Ixox/preenfm2/src/synth/Timbre.cpp

/*
 * Copyright 2013 Xavier Hosxe
 *
 * Author: Xavier Hosxe (xavier <.> hosxe < a t > gmail.com)
 *
 * This program is free software: you can redistribute it and/or modify
 * it under the terms of the GNU General Public License as published by
 * the Free Software Foundation, either version 3 of the License, or
 * (at your option) any later version.
 * This program is distributed in the hope that it will be useful,
 * but WITHOUT ANY WARRANTY; without even the implied warranty of
 * MERCHANTABILITY or FITNESS FOR A PARTICULAR PURPOSE.  See the
 * GNU General Public License for more details.
 * You should have received a copy of the GNU General Public License
 * along with this program.  If not, see <http://www.gnu.org/licenses/>.
 */


#include <math.h>
#include "Timbre.h"
#include "Voice.h"

#define INV127 .00787401574803149606f
#define INV16 .0625f
#define filterWindowMin 0.01f
#define filterWindowMax 0.99f
// Regular memory
float midiNoteScale[2][NUMBER_OF_TIMBRES][128];

float Timbre::unisonPhase[14] = { .37f, .11f, .495f, .53f, .03f, .19f, .89f, 0.23f, .71f, .19f, .31f, .43f, .59f, .97f };

/*
#include "LiquidCrystal.h"
extern LiquidCrystal lcd;
void myVoiceError(char info, int t, int t2) {
    lcd.setRealTimeAction(true);
    lcd.clear();
    lcd.setCursor(0,0);
    lcd.print('!');
    lcd.print(info);
    lcd.print(t);
    lcd.print(' ');
    lcd.print(t2);
    while (true) {};
}

...
        if (voiceNumber[k] < 0) myVoiceError('A', voiceNumber[k], k);

*/

//#define DEBUG_ARP_STEP
enum ArpeggiatorDirection {
    ARPEGGIO_DIRECTION_UP = 0,
    ARPEGGIO_DIRECTION_DOWN,
    ARPEGGIO_DIRECTION_UP_DOWN,
    ARPEGGIO_DIRECTION_PLAYED,
    ARPEGGIO_DIRECTION_RANDOM,
    ARPEGGIO_DIRECTION_CHORD,
   /*
    * ROTATE modes rotate the first note played, e.g. UP: C-E-G -> E-G-C -> G-C-E -> repeat
    */
    ARPEGGIO_DIRECTION_ROTATE_UP, ARPEGGIO_DIRECTION_ROTATE_DOWN, ARPEGGIO_DIRECTION_ROTATE_UP_DOWN,
   /*
    * SHIFT modes rotate and extend with transpose, e.g. UP: C-E-G -> E-G-C1 -> G-C1-E1 -> repeat
    */
    ARPEGGIO_DIRECTION_SHIFT_UP, ARPEGGIO_DIRECTION_SHIFT_DOWN, ARPEGGIO_DIRECTION_SHIFT_UP_DOWN,

    ARPEGGIO_DIRECTION_COUNT
};

// TODO Maybe add something like struct ArpDirectionParams { dir, can_change, use_start_step }

inline static int __getDirection( int _direction ) {
	switch( _direction ) {
	case ARPEGGIO_DIRECTION_DOWN:
	case ARPEGGIO_DIRECTION_ROTATE_DOWN:
	case ARPEGGIO_DIRECTION_SHIFT_DOWN:
		return -1;
	default:
		return 1;
	}
}

inline static int __canChangeDir( int _direction ) {
	switch( _direction ) {
	case ARPEGGIO_DIRECTION_UP_DOWN:
	case ARPEGGIO_DIRECTION_ROTATE_UP_DOWN:
	case ARPEGGIO_DIRECTION_SHIFT_UP_DOWN:
		return 1;
	default:
		return 0;
	}
}

inline static int __canTranspose( int _direction ) {
	switch( _direction ) {
	case ARPEGGIO_DIRECTION_SHIFT_UP:
	case ARPEGGIO_DIRECTION_SHIFT_DOWN:
	case ARPEGGIO_DIRECTION_SHIFT_UP_DOWN:
		return 1;
	default:
		return 0;
	}
}

//for bitwise manipulations
#define FLOAT2SHORT 32768.f
#define SHORT2FLOAT 1./32768.f

#define RATIOINV 1./131072.f

#define SVFRANGE 1.23f
#define SVFOFFSET 0.151f
#define SVFGAINOFFSET 0.3f

#define LP2OFFSET -0.045f
#define min(a,b)                ((a)<(b)?(a):(b))
#define PIINV 0.318309886183791f

extern float noise[32];

inline 
float expf_fast(float a) {
  //https://github.com/ekmett/approximate/blob/master/cbits/fast.c
  union { float f; int x; } u;
  u.x = (int) (12102203 * a + 1064866805);
  return u.f;
}
inline
float sqrt3(const float x)  
{
  union
  {
    int i;
    float x;
  } u;

  u.x = x;
  u.i = (1 << 29) + (u.i >> 1) - (1 << 22);
  return u.x;
} 
inline
float tanh3(float x)
{
	//return x / (0.7f + fabsf(0.8f * x));
	return 1.5f * x / (1.7f + fabsf(0.34f * x * x));
}
inline
float tanh4(float x)
{
	return x / sqrt3(x * x + 1);
}
inline
float sat25(float x)
{ 
	if (unlikely(fabsf(x) > 4))
		return 0;
	return x * (1.f - fabsf(x * 0.25f));
}
inline
float sat66(float x)
{
	return x * (1 - (x * x * 0.055f));
}
inline
float sat33(float x)
{
	if (unlikely(fabsf(x) > 2.58f))
		return 0;
	return x * (1 - x * x * 0.15f);
}
inline
float clamp(float d, float min, float max) {
  const float t = unlikely(d < min) ? min : d;
  return unlikely(t > max) ? max : t;
}
inline 
float satSin(float x, float drive, uint_fast16_t pos) {
	//https://www.desmos.com/calculator/pdsqpi5lp6
	return x + clamp(x, -0.5f * drive, drive) * sinTable[((uint_fast16_t)(fabsf(x) * 360) + pos) & 0x3FF];
}
inline 
float fastSin(float x) {
	return sinTable[(int)(fabsf(x * PIINV) * 2048)  & 0x7FF] * 0.5f;
}
//https://www.musicdsp.org/en/latest/Other/120-saturation.html
inline
float sigmoid(float x)
{
	return x * (1.5f - 0.5f * x * x);
}
inline
float sigmoidPos(float x)
{
	//x : 0 -> 1
	return (sigmoid((x * 2) - 1) + 1) * 0.5f;
}
inline
float fold(float x4) {
	// https://www.desmos.com/calculator/ge2wvg2wgj
	// x4 = x / 4
	return (fabsf(x4 + 0.25f - roundf(x4 + 0.25f)) - 0.25f);
}
inline
float foldPos(float x) {
	return fold(((x * 2) - 1) * 0.25f) * 2 + 0.5f;
}
inline
float wrap(float x) {
	return x - floorf(x);
}
inline
float wrapBipolar(float x) {
	const float a = fabsf(x);
	return copysignf(a - floorf(a), x);
}
inline 
float window(float x) {
	if (x < 0 || x > 1) {
		return 0;
	} else if (x < 0.2f) {
		return sqrt3( x * 5 );
	} else if (x > 0.8f) {
		return sqrt3(1 - (x-0.8f) * 5);
	} else {
		return 1;
	}
}
inline float ftan(float fAngle)
{
	float fASqr = fAngle * fAngle;
	float fResult = 2.033e-01f;
	fResult *= fASqr;
	fResult += 3.1755e-01f;
	fResult *= fASqr;
	fResult += 1.0f;
	fResult *= fAngle;
	return fResult;
}
enum NewNoteType {
	NEW_NOTE_FREE = 0,
	NEW_NOTE_RELEASE,
	NEW_NOTE_OLD,
	NEW_NOTE_NONE
};
//TB303 filter emulation ------
const float filterpoles[10][64] = {
	{-1.42475857e-02, -1.10558351e-02, -9.58097367e-03,
	 -8.63568249e-03, -7.94942757e-03, -7.41570560e-03,
	 -6.98187179e-03, -6.61819537e-03, -6.30631927e-03,
	 -6.03415378e-03, -5.79333654e-03, -5.57785533e-03,
	 -5.38325013e-03, -5.20612558e-03, -5.04383985e-03,
	 -4.89429884e-03, -4.75581571e-03, -4.62701254e-03,
	 -4.50674977e-03, -4.39407460e-03, -4.28818259e-03,
	 -4.18838855e-03, -4.09410427e-03, -4.00482112e-03,
	 -3.92009643e-03, -3.83954259e-03, -3.76281836e-03,
	 -3.68962181e-03, -3.61968451e-03, -3.55276681e-03,
	 -3.48865386e-03, -3.42715236e-03, -3.36808777e-03,
	 -3.31130196e-03, -3.25665127e-03, -3.20400476e-03,
	 -3.15324279e-03, -3.10425577e-03, -3.05694308e-03,
	 -3.01121207e-03, -2.96697733e-03, -2.92415989e-03,
	 -2.88268665e-03, -2.84248977e-03, -2.80350622e-03,
	 -2.76567732e-03, -2.72894836e-03, -2.69326825e-03,
	 -2.65858922e-03, -2.62486654e-03, -2.59205824e-03,
	 -2.56012496e-03, -2.52902967e-03, -2.49873752e-03,
	 -2.46921570e-03, -2.44043324e-03, -2.41236091e-03,
	 -2.38497108e-03, -2.35823762e-03, -2.33213577e-03,
	 -2.30664208e-03, -2.28173430e-03, -2.25739130e-03,
	 -2.23359302e-03},
	{1.63323670e-16, -1.61447133e-02, -1.99932070e-02,
	 -2.09872000e-02, -2.09377795e-02, -2.04470150e-02,
	 -1.97637613e-02, -1.90036975e-02, -1.82242987e-02,
	 -1.74550383e-02, -1.67110053e-02, -1.59995606e-02,
	 -1.53237941e-02, -1.46844019e-02, -1.40807436e-02,
	 -1.35114504e-02, -1.29747831e-02, -1.24688429e-02,
	 -1.19916965e-02, -1.15414484e-02, -1.11162818e-02,
	 -1.07144801e-02, -1.03344362e-02, -9.97465446e-03,
	 -9.63374867e-03, -9.31043725e-03, -9.00353710e-03,
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


    // Init FX variables
	v0L = v1L = v2L = v3L = v4L = v5L = v6L = v7L = v8L = v0R = v1R = v2R = v3R = v4R = v5R = v6R = v7R = v8R = v8R = 0.0f;
	fxParamA1 = fxParamA2 = fxParamB2 = 0;
    fxParam1PlusMatrix = -1.0;

	// Center balance
	leftRightBalance = .5f;

}

Timbre::~Timbre() {
}

void Timbre::init(int timbreNumber, SynthState* sState) {


	env1.init(&params.env1a,  &params.env1b, 0, &params.engine1.algo);
	env2.init(&params.env2a,  &params.env2b, 1, &params.engine1.algo);
	env3.init(&params.env3a,  &params.env3b, 2, &params.engine1.algo);
	env4.init(&params.env4a,  &params.env4b, 3, &params.engine1.algo);
	env5.init(&params.env5a,  &params.env5b, 4, &params.engine1.algo);
	env6.init(&params.env6a,  &params.env6b, 5, &params.engine1.algo);

	osc1.init(sState, &params.osc1, OSC1_FREQ);
	osc2.init(sState, &params.osc2, OSC2_FREQ);
	osc3.init(sState, &params.osc3, OSC3_FREQ);
	osc4.init(sState, &params.osc4, OSC4_FREQ);
	osc5.init(sState, &params.osc5, OSC5_FREQ);
	osc6.init(sState, &params.osc6, OSC6_FREQ);

    this->timbreNumber = timbreNumber;

    for (int s=0; s<2; s++) {
        for (int n=0; n<128; n++) {
            midiNoteScale[s][timbreNumber][n] = INV127 * (float)n;
        }
    }
    for (int lfo=0; lfo<NUMBER_OF_LFO; lfo++) {
        lfoUSed[lfo] = 0;
    }

}

void Timbre::setVoiceNumber(int v, int n) {
	voiceNumber[v] = n;
	if (n >=0) {
		voices[n]->setCurrentTimbre(this);
	}
}


void Timbre::initVoicePointer(int n, Voice* voice) {
	voices[n] = voice;
}

void Timbre::noteOn(uint8_t note, uint8_t velocity) {
	if (params.engineArp1.clock) {
		arpeggiatorNoteOn(note, velocity);
	} else {
		preenNoteOn(note, velocity);
	}
}

void Timbre::noteOff(uint8_t note) {
	if (params.engineArp1.clock) {
		arpeggiatorNoteOff(note);
	} else {
		preenNoteOff(note);
	}
}

int cptHighNote = 0;

void Timbre::preenNoteOn(uint8_t note, uint8_t velocity) {

	this->lastVelocity = velocity * INV127;
	bool isUnison = params.engine1.numberOfVoice > 1  && params.engine2.playMode == 2.0f;

	int iNov;
	if (likely(!isUnison)) {
		iNov = (int) params.engine1.numberOfVoice;
	} else {
		iNov = 1;
	}

	if (unlikely(iNov == 0)) {
		return;
	}

	unsigned int indexMin = (unsigned int)2147483647;
	int voiceToUse = -1;

	int newNoteType = NEW_NOTE_NONE;

	for (int k = 0; k < iNov; k++) {
		// voice number k of timbre
		int n = voiceNumber[k];

        if (unlikely(voices[n]->isNewNotePending())) {
            continue;
        }

		// same note = priority 1 : take the voice immediatly
		if (unlikely(voices[n]->isPlaying() && voices[n]->getNote() == note)) {

#ifdef DEBUG_VOICE
		lcd.setRealTimeAction(true);
		lcd.setCursor(16,1);
		lcd.print(cptHighNote++);
		lcd.setCursor(16,2);
		lcd.print("S:");
		lcd.print(n);
#endif
			if (!isUnison) {
				preenNoteOnUpdateMatrix(n, note, velocity);
				voices[n]->noteOnWithoutPop(note, velocity, voiceIndex++);
			} else {
				float noteFrequencyUnison = (1 - params.engine2.unisonDetune * .05f);
				float noteFrequencyUnisonInc =  params.engine2.unisonDetune * numberOfVoiceInverse * .1f;

                for (int k = 0; k < params.engine1.numberOfVoice; k++) {
                    int n = voiceNumber[k];
                    preenNoteOnUpdateMatrix(n, note, velocity);
                    voices[n]->noteOnWithoutPop(note, velocity, voiceIndex++, noteFrequencyUnison, unisonPhase[k]);
					noteFrequencyUnison += noteFrequencyUnisonInc;
                }
			}
			this->lastPlayedVoiceNum = n;
			return;
		}

		// unlikely because if it true, CPU is not full
		if (unlikely(newNoteType > NEW_NOTE_FREE)) {
			if (!voices[n]->isPlaying()) {
				voiceToUse = n;
				newNoteType = NEW_NOTE_FREE;
			} else if (voices[n]->isReleased()) {
				int indexVoice = voices[n]->getIndex();
				if (indexVoice < indexMin) {
					indexMin = indexVoice;
					voiceToUse = n;
					newNoteType = NEW_NOTE_RELEASE;
				}
			}
		}
	}

	if (voiceToUse == -1) {
		for (int k = 0; k < iNov; k++) {
			// voice number k of timbre
			int n = voiceNumber[k];
			int indexVoice = voices[n]->getIndex();
			if (indexVoice < indexMin && !voices[n]->isNewNotePending()) {
				newNoteType = NEW_NOTE_OLD;
				indexMin = indexVoice;
				voiceToUse = n;
			}
		}
	}
	// All voices in newnotepending state ?
	if (voiceToUse != -1) {

		if (!isUnison) {
			preenNoteOnUpdateMatrix(voiceToUse, note, velocity);

			switch (newNoteType) {
			case NEW_NOTE_FREE:
				voices[voiceToUse]->noteOn(note, velocity, voiceIndex++);
				break;
			case NEW_NOTE_OLD:
			case NEW_NOTE_RELEASE:
				voices[voiceToUse]->noteOnWithoutPop(note, velocity, voiceIndex++);
				break;
			}

		} else {
            // Unisons : we start all voices with different frequency

			float noteFrequencyUnison = (1 - params.engine2.unisonDetune * .05f);
			float noteFrequencyUnisonInc =  params.engine2.unisonDetune * numberOfVoiceInverse * .1f;

			for (int k = 0; k < params.engine1.numberOfVoice; k++) {

				int n = voiceNumber[k];
				preenNoteOnUpdateMatrix(n, note, velocity);

				switch (newNoteType) {
				case NEW_NOTE_FREE:
					voices[n]->noteOn(note, velocity, voiceIndex++, noteFrequencyUnison, unisonPhase[k]);
					break;
				case NEW_NOTE_OLD:
				case NEW_NOTE_RELEASE:
					voices[n]->noteOnWithoutPop(note, velocity, voiceIndex++, noteFrequencyUnison, unisonPhase[k]);
					break;
				}
				noteFrequencyUnison += noteFrequencyUnisonInc;
			}
		}
		lastPlayedVoiceNum = voiceToUse;
	}
}

void Timbre::preenNoteOnUpdateMatrix(int voiceToUse, int note, int velocity) {
    // Update voice matrix with midi note and velocity
    if (likely(note < 128)) {
        voices[voiceToUse]->matrix.setSource(MATRIX_SOURCE_NOTE1, midiNoteScale[0][timbreNumber][note]);
        voices[voiceToUse]->matrix.setSource(MATRIX_SOURCE_NOTE2, midiNoteScale[1][timbreNumber][note]);
        voices[voiceToUse]->matrix.setSource(MATRIX_SOURCE_VELOCITY, INV127*velocity);
    }

    voices[voiceToUse]->matrix.setSource(MATRIX_SOURCE_RANDOM, noise[voiceToUse]);

	if (unlikely(this->seqStartUsed[0] != 0xFF)) {
		voices[voiceToUse]->matrix.computeOneDestination(seqStartUsed[0]);
	}
	if (unlikely(this->seqStartUsed[1] != 0xFF)) {
		// No need to recalculte if it's the same row as the other one
		if (seqStartUsed[0] != seqStartUsed[1]) {
			voices[voiceToUse]->matrix.computeOneDestination(seqStartUsed[1]);
		}
	}
}


#ifdef CVIN
void Timbre::propagateCvFreq(uint8_t note) {
	bool isUnison = params.engine1.numberOfVoice > 1  && params.engine2.playMode == 2.0f;
    int iNov = (int) params.engine1.numberOfVoice;
    for (int k = 0; k < iNov; k++) {
        int n = voiceNumber[k];
        if (voices[n]->getNote() == note) {
            if (voices[n]->isPlaying()) {
                voices[n]->propagateCvFreq(note);
            }
            if (!isUnison) {
                return;
            }
        }
    }
}
#endif

void Timbre::preenNoteOff(uint8_t note) {
	bool isUnison = params.engine1.numberOfVoice > 1  && params.engine2.playMode == 2.0f;

	int iNov = (int) params.engine1.numberOfVoice;
	for (int k = 0; k < iNov; k++) {
		// voice number k of timbre
		int n = voiceNumber[k];

		// Not playing = free CPU
		if (unlikely(!voices[n]->isPlaying())) {
			continue;
		}

		if (likely(voices[n]->getNextGlidingNote() == 0)) {
			if (voices[n]->getNote() == note) {
				if (unlikely(holdPedal)) {
					voices[n]->setHoldedByPedal(true);
					if (likely(!isUnison)) {
						return;
					}
				} else {
					voices[n]->noteOff();
					if (likely(!isUnison)) {
						return;
					}
				}
			}
		} else {
			// if gliding and releasing first note
			if (voices[n]->getNote() == note) {
				voices[n]->glideFirstNoteOff();
				if (likely(!isUnison)) {
					return;
				}
			}
			// if gliding and releasing next note
			if (voices[n]->getNextGlidingNote() == note) {
				voices[n]->glideToNote(voices[n]->getNote());
				voices[n]->glideFirstNoteOff();
				if (likely(!isUnison)) {
					return;
				}
			}
		}
	}
}

void Timbre::stopPlayingNow() {
	int iNov = (int) params.engine1.numberOfVoice;
	for (int k = 0; k < iNov; k++) {
		// voice number k of timbre
		int n = voiceNumber[k];
        if (n != -1) {
            voices[n]->killNow();
        }
    }
}


void Timbre::setHoldPedal(int value) {
	if (value <64) {
		holdPedal = false;
	    int numberOfVoices = params.engine1.numberOfVoice;
	    for (int k = 0; k < numberOfVoices; k++) {
	        // voice number k of timbre
	        int n = voiceNumber[k];
	        if (voices[n]->isHoldedByPedal()) {
	        	voices[n]->noteOff();
	        }
	    }
	    arpeggiatorSetHoldPedal(0);
	} else {
		holdPedal = true;
	    arpeggiatorSetHoldPedal(127);
	}
}




void Timbre::setNewBPMValue(float bpm) {
	ticksPerSecond = bpm * 24.0f / 60.0f;

	float calledPerSecond = PREENFM_FREQUENCY / 32.0f;
	ticksEveryNCalls = calledPerSecond / ticksPerSecond;
	ticksEveyNCallsInteger = (int)ticksEveryNCalls;
}

void Timbre::setArpeggiatorClock(float clockValue) {
	if (clockValue == CLOCK_OFF) {
		FlushQueue();
		note_stack.Clear();
	}
	if (clockValue == CLOCK_INTERNAL) {
	    setNewBPMValue(params.engineArp1.BPM);
	}
	if (clockValue == CLOCK_EXTERNAL) {
		// Let's consider we're running
		running_ = 1;
	}
}


void Timbre::prepareForNextBlock() {

	// Apeggiator clock : internal
	if (params.engineArp1.clock == CLOCK_INTERNAL) {
		arpegiatorStep+=1.0f;
		if (unlikely((arpegiatorStep) > ticksEveryNCalls)) {
			arpegiatorStep -= ticksEveyNCallsInteger;
			Tick();
		}
	}
}

void Timbre::cleanNextBlock() {

	float *sp = this->sampleBlock;
	while (sp < this->sbMax) {
		*sp++ = 0;
		*sp++ = 0;
		*sp++ = 0;
		*sp++ = 0;
		*sp++ = 0;
		*sp++ = 0;
		*sp++ = 0;
		*sp++ = 0;
	}
}


void Timbre::prepareMatrixForNewBlock() {
    for (int k = 0; k < params.engine1.numberOfVoice; k++) {
		// Can be -1 during preset load
		if (likely(voiceNumber[k] != -1)) {
	        voices[voiceNumber[k]]->prepareMatrixForNewBlock();
		}
    }
}

uint8_t Timbre::voicesNextBlock() {
    uint8_t numberOfPlayingVoices = 0;
	bool isUnison = params.engine1.numberOfVoice > 1  && params.engine2.playMode == 2.0f;
    if (unlikely(!isUnison)) {
		for (int k = 0; k < params.engine1.numberOfVoice; k++) {
			int n = voiceNumber[k];
			if (likely(n >= 0 && this->voices[n]->isPlaying())) {
				this->voices[n]->nextBlock();
				numberOfPlayingVoices ++;
			}
		}
	} else {
        // UNISON
        float pansSav[6];
        pansSav[0] = params.engineMix1.panOsc1;
        pansSav[1] = params.engineMix1.panOsc2;
        pansSav[2] = params.engineMix2.panOsc3;
        pansSav[3] = params.engineMix2.panOsc4;
        pansSav[4] = params.engineMix3.panOsc5;
        pansSav[5] = params.engineMix3.panOsc6;

        float* pans[] = {
            &params.engineMix1.panOsc1,
            &params.engineMix1.panOsc2,
            &params.engineMix2.panOsc3,
            &params.engineMix2.panOsc4,
            &params.engineMix3.panOsc5,
            &params.engineMix3.panOsc6
        };

		int currentAlgo = (int)params.engine1.algo;
        int algoNumberOfMix = algoInformation[currentAlgo].mix;
		int numberOfVoices = params.engine1.numberOfVoice;
        float numberOfCarrierOp = numberOfVoices * algoNumberOfMix;
        float opPan = - params.engine2.unisonSpread;
        float opPanInc = 2.0f / numberOfCarrierOp * params.engine2.unisonSpread;

        if (likely(voiceNumber[0] >=0 && voices[voiceNumber[0]]->isPlaying())) {
            for (int vv = 0; vv < numberOfVoices; vv++) {
                int v = voiceNumber[vv];
				if (unlikely(v < 0)) {
					continue;
				}
				bool otherSide = false;
                for (int op = 0; op < 6; op ++) {
					if (algoOpInformation[currentAlgo][op] == 1) {
						if (otherSide) {
							*pans[op] = -opPan;
						} else {
							*pans[op] = opPan;
						}
	                    opPan += opPanInc;
						otherSide =! otherSide;
					}
                }
                voices[v]->nextBlock();
                numberOfPlayingVoices++;
            }
        }

        params.engineMix1.panOsc1 = pansSav[0];
        params.engineMix1.panOsc2 = pansSav[1];
        params.engineMix2.panOsc3 = pansSav[2];
        params.engineMix2.panOsc4 = pansSav[3];
        params.engineMix3.panOsc5 = pansSav[4];
        params.engineMix3.panOsc6 = pansSav[5];
	}
	return numberOfPlayingVoices;
}

void Timbre::glide() {
	bool isUnison = params.engine1.numberOfVoice > 1  && params.engine2.playMode == 2.0f;
    if (unlikely(!isUnison)) {
		// need to glide ?
		if (voiceNumber[0] >= 0 && this->voices[voiceNumber[0]]->isGliding()) {
			this->voices[voiceNumber[0]]->glide();
		}
	} else {
        for (int vv = 0; vv < params.engine1.numberOfVoice; vv++) {
            int v = voiceNumber[vv];
            if (v >= 0 && voices[v]->isGliding()) {
                voices[v]->glide();
            }
        }
	}
}

#define GATE_INC 0.02f

void Timbre::fxAfterBlock(float ratioTimbres) {

    // Gate algo !!
    float gate = voices[this->lastPlayedVoiceNum]->matrix.getDestination(MAIN_GATE);
    if (unlikely(gate > 0 || currentGate > 0)) {
		gate *=.72547132656922730694f; // 0 < gate < 1.0
		if (gate > 1.0f) {
			gate = 1.0f;
		}
		float incGate = (gate - currentGate) * .03125f; // ( *.03125f = / 32)
		// limit the speed.
		if (incGate > 0.002f) {
			incGate = 0.002f;
		} else if (incGate < -0.002f) {
			incGate = -0.002f;
		}

		float *sp = this->sampleBlock;
		float coef;
    	for (int k=0 ; k< BLOCK_SIZE ; k++) {
			currentGate += incGate;
			coef = 1.0f - currentGate;
			*sp = *sp * coef;
			sp++;
			*sp = *sp * coef;
			sp++;
		}
    //    currentGate = gate;
    }

    float matrixFilterFrequency = voices[this->lastPlayedVoiceNum]->matrix.getDestination(FILTER_FREQUENCY);
	float numberVoicesAttn = 1 - (params.engine1.numberOfVoice * 0.04f * ratioTimbres * RATIOINV);

    // LP Algo
    int effectType = params.effect.type;
    float gainTmp =  params.effect.param3 * numberOfVoiceInverse * ratioTimbres;
    mixerGain = 0.02f * gainTmp + .98f  * mixerGain;

    switch (effectType) {
    case FILTER_LP:
    {
    	float fxParamTmp = params.effect.param1 + matrixFilterFrequency;
    	fxParamTmp *= fxParamTmp;

    	// Low pass... on the Frequency
    	fxParam1 = (fxParamTmp + 9.0f * fxParam1) * .1f;
    	if (unlikely(fxParam1 > 1.0f)) {
    		fxParam1 = 1.0f;
    	}
    	if (unlikely(fxParam1 < 0.0f)) {
    		fxParam1 = 0.0f;
    	}

    	float pattern = (1 - fxParam2 * fxParam1);

    	float *sp = this->sampleBlock;
    	float localv0L = v0L;
    	float localv1L = v1L;
    	float localv0R = v0R;
    	float localv1R = v1R;

    	for (int k=BLOCK_SIZE ; k--; ) {

    		// Left voice
    		localv0L =  pattern * localv0L  -  (fxParam1) * (localv1L + *sp);
    		localv1L =  pattern * localv1L  +  (fxParam1) * localv0L;

    		*sp = localv1L * mixerGain;

    		if (unlikely(*sp > ratioTimbres)) {
    			*sp = ratioTimbres;
    		}
    		if (unlikely(*sp < -ratioTimbres)) {
    			*sp = -ratioTimbres;
    		}

    		sp++;

    		// Right voice
    		localv0R =  pattern * localv0R  -  (fxParam1) * (localv1R + *sp);
    		localv1R =  pattern * localv1R  +  (fxParam1) * localv0R;

    		*sp = localv1R * mixerGain;

    		if (unlikely(*sp > ratioTimbres)) {
    			*sp = ratioTimbres;
    		}
    		if (unlikely(*sp < -ratioTimbres)) {
    			*sp = -ratioTimbres;
    		}

    		sp++;
    	}
    	v0L = localv0L;
    	v1L = localv1L;
    	v0R = localv0R;
    	v1R = localv1R;
    }
    break;
    case FILTER_HP:
    {
    	float fxParamTmp = params.effect.param1 + matrixFilterFrequency;
    	fxParamTmp *= fxParamTmp;

    	// Low pass... on the Frequency
    	fxParam1 = (fxParamTmp + 9.0f * fxParam1) * .1f;
    	if (unlikely(fxParam1 > 1.0)) {
    		fxParam1 = 1.0;
    	}
        if (unlikely(fxParam1 < 0.0f)) {
            fxParam1 = 0.0f;
        }
    	float pattern = (1 - fxParam2 * fxParam1);

    	float *sp = this->sampleBlock;
    	float localv0L = v0L;
    	float localv1L = v1L;
    	float localv0R = v0R;
    	float localv1R = v1R;

    	for (int k=0 ; k < BLOCK_SIZE ; k++) {

    		// Left voice
    		localv0L =  pattern * localv0L  -  (fxParam1) * localv1L  + (fxParam1) * (*sp);
    		localv1L =  pattern * localv1L  +  (fxParam1) * localv0L;

    		*sp = (*sp - localv1L) * mixerGain;

    		if (unlikely(*sp > ratioTimbres)) {
    			*sp = ratioTimbres;
    		}
    		if (unlikely(*sp < -ratioTimbres)) {
    			*sp = -ratioTimbres;
    		}

    		sp++;

    		// Right voice
    		localv0R =  pattern * localv0R  -  (fxParam1) * localv1R  + (fxParam1) * (*sp);
    		localv1R =  pattern * localv1R  +  (fxParam1) * localv0R;

    		*sp = (*sp - localv1R) * mixerGain;

    		if (unlikely(*sp > ratioTimbres)) {
    			*sp = ratioTimbres;
    		}
    		if (unlikely(*sp < -ratioTimbres)) {
    			*sp = -ratioTimbres;
    		}

    		sp++;
    	}
    	v0L = localv0L;
    	v1L = localv1L;
    	v0R = localv0R;
    	v1R = localv1R;

    }
	break;
    case FILTER_BASS:
    {
    	// From musicdsp.com
    	//    	Bass Booster
    	//
    	//    	Type : LP and SUM
    	//    	References : Posted by Johny Dupej
    	//
    	//    	Notes :
    	//    	This function adds a low-passed signal to the original signal. The low-pass has a quite wide response.
    	//
    	//    	selectivity - frequency response of the LP (higher value gives a steeper one) [70.0 to 140.0 sounds good]
    	//    	ratio - how much of the filtered signal is mixed to the original
    	//    	gain2 - adjusts the final volume to handle cut-offs (might be good to set dynamically)

    	//static float selectivity, gain1, gain2, ratio, cap;
    	//gain1 = 1.0/(selectivity + 1.0);
    	//
    	//cap= (sample + cap*selectivity )*gain1;
    	//sample = saturate((sample + cap*ratio)*gain2);

    	float *sp = this->sampleBlock;
    	float localv0L = v0L;
    	float localv0R = v0R;

    	for (int k=0 ; k < BLOCK_SIZE ; k++) {

    		localv0L = ((*sp) + localv0L * fxParam1) * fxParam3;
    		(*sp) = ((*sp) + localv0L * fxParam2) * mixerGain;

    		if (unlikely(*sp > ratioTimbres)) {
    			*sp = ratioTimbres;
    		}
    		if (unlikely(*sp < -ratioTimbres)) {
    			*sp = -ratioTimbres;
    		}

    		sp++;

    		localv0R = ((*sp) + localv0R * fxParam1) * fxParam3;
    		(*sp) = ((*sp) + localv0R * fxParam2) * mixerGain;

    		if (unlikely(*sp > ratioTimbres)) {
    			*sp = ratioTimbres;
    		}
    		if (unlikely(*sp < -ratioTimbres)) {
    			*sp = -ratioTimbres;
    		}

    		sp++;
    	}
    	v0L = localv0L;
    	v0R = localv0R;

    }
    break;
    case FILTER_MIXER:
    {
		float fxParamTmp = params.effect.param1 + matrixFilterFrequency;
		// Low pass... on the Frequency
		fxParam1 = clamp((fxParamTmp + 9.0f * fxParam1) * .1f, 0, 1);

    	float pan = fxParam1 * 2 - 1.0f ;
    	float *sp = this->sampleBlock;
    	float sampleR, sampleL;
    	if (pan <= 0) {
        	float onePlusPan = 1 + pan;
        	float minusPan = - pan;
        	for (int k=BLOCK_SIZE ; k--; ) {
				sampleL = *(sp);
				sampleR = *(sp + 1);

				*sp = (sampleL + sampleR * minusPan) * mixerGain;
				sp++;
				*sp = sampleR * onePlusPan * mixerGain;
				sp++;
			}
    	} else if (pan > 0) {
        	float oneMinusPan = 1 - pan;
        	for (int k=0 ; k < BLOCK_SIZE ; k++) {
				sampleL = *(sp);
				sampleR = *(sp + 1);

				*sp = sampleL * oneMinusPan * mixerGain;
				sp++;
				*sp = (sampleR + sampleL * pan) * mixerGain;
				sp++;
			}
    	}
    }
    break;
    case FILTER_CRUSHER:
    {
        // Algo from http://www.musicdsp.org/archive.php?classid=4#139
        // Lo-Fi Crusher
        // Type : Quantizer / Decimator with smooth control
        // References : Posted by David Lowenfels

        //        function output = crusher( input, normfreq, bits );
        //            step = 1/2^(bits);
        //            phasor = 0;
        //            last = 0;
        //
        //            for i = 1:length(input)
        //               phasor = phasor + normfreq;
        //               if (phasor >= 1.0)
        //                  phasor = phasor - 1.0;
        //                  last = step * floor( input(i)/step + 0.5 ); %quantize
        //               end
        //               output(i) = last; %sample and hold
        //            end
        //        end


        float fxParamTmp = params.effect.param1 + matrixFilterFrequency +.005f;
        if (unlikely(fxParamTmp > 1.0)) {
            fxParamTmp = 1.0;
        }
        if (unlikely(fxParamTmp < 0.005f)) {
            fxParamTmp = 0.005f;
        }
        fxParamA1 = (fxParamTmp + 9.0f * fxParamA1) * .1f;
        // Low pass... on the Sampling rate
        register float fxFreq = fxParamA1;

        register float *sp = this->sampleBlock;

        register float localPhase = v7R;

        //        localPower = fxParam1 = pow(2, (int)(1.0f + 15.0f * params.effect.param2));
        //        localStep = fxParam2 = 1 / fxParam1;

        register float localPower = fxParam1;
        register float localStep = fxParam2;

        register float localv0L = v0L;
        register float localv0R = v0R;


        for (int k=0 ; k < BLOCK_SIZE ; k++) {
            localPhase += fxFreq;
            if (unlikely(localPhase >= 1.0f)) {
                localPhase -= 1.0f;
                // Simulate floor by making the conversion always positive
                // simplify version
                register int iL =  (*sp) * localPower + .75f;
                register int iR =  (*(sp + 1)) * localPower + .75f;
                localv0L = localStep * iL;
                localv0R = localStep * iR;
            }

            *sp++ = localv0L * mixerGain;
            *sp++ = localv0R * mixerGain;
        }
        v0L = localv0L;
        v0R = localv0R;
        v7R = localPhase;

    }
    break;
    case FILTER_BP:
    {
//        float input;                    // input sample
//        float output;                   // output sample
//        float v;                        // This is the intermediate value that
//                                        //    gets stored in the delay registers
//        float old1;                     // delay register 1, initialized to 0
//        float old2;                     // delay register 2, initialized to 0
//
//        /* filter coefficients */
//        omega1  = 2 * PI * f/srate; // f is your center frequency
//        sn1 = (float)sin(omega1);
//        cs1 = (float)cos(omega1);
//        alpha1 = sn1/(2*Qvalue);        // Qvalue is none other than Q!
//        a0 = 1.0f + alpha1;     // a0
//        b0 = alpha1;            // b0
//        b1 = 0.0f;          // b1/b0
//        b2= -alpha1/b0          // b2/b0
//        a1= -2.0f * cs1/a0;     // a1/a0
//        a2= (1.0f - alpha1)/a0;          // a2/a0
//        k = b0/a0;
//
//        /* The filter code */
//
//        v = k*input - a1*old1 - a2*old2;
//        output = v + b1*old1 + b2*old2;
//        old2 = old1;
//        old1 = v;

        // fxParam1 v
        //

        float fxParam1PlusMatrixTmp = params.effect.param1 + matrixFilterFrequency;
        if (unlikely(fxParam1PlusMatrixTmp > 1.0f)) {
            fxParam1PlusMatrixTmp = 1.0f;
        }
        if (unlikely(fxParam1PlusMatrixTmp < 0.0f)) {
            fxParam1PlusMatrixTmp = 0.0f;
        }

		if (fxParam1PlusMatrix != fxParam1PlusMatrixTmp) {
			fxParam1PlusMatrix = fxParam1PlusMatrixTmp;
			recomputeBPValues(params.effect.param2, fxParam1PlusMatrix * fxParam1PlusMatrix);
		}

        float localv0L = v0L;
        float localv0R = v0R;
        float localv1L = v1L;
        float localv1R = v1R;
        float *sp = this->sampleBlock;

        for (int k=0 ; k < BLOCK_SIZE ; k++) {
            float localV = fxParam1 /* k */ * (*sp) - fxParamA1 * localv0L - fxParamA2 * localv1L;
            *sp++ = (localV + /* fxParamB1 (==0) * localv0L  + */ fxParamB2 * localv1L) * mixerGain;
            if (unlikely(*sp > ratioTimbres)) {
                *sp = ratioTimbres;
            }
            if (unlikely(*sp < -ratioTimbres)) {
                *sp = -ratioTimbres;
            }
            localv1L = localv0L;
            localv0L = localV;

            localV = fxParam1 /* k */ * (*sp) - fxParamA1 * localv0R - fxParamA2 * localv1R;
            *sp++ = (localV + /* fxParamB1 (==0) * localv0R + */ fxParamB2 * localv1R) * mixerGain;
            if (unlikely(*sp > ratioTimbres)) {
                *sp = ratioTimbres;
            }
            if (unlikely(*sp < -ratioTimbres)) {
                *sp = -ratioTimbres;
            }
            localv1R = localv0R;
            localv0R = localV;


        }

        v0L = localv0L;
        v0R = localv0R;
        v1L = localv1L;
        v1R = localv1R;

        break;
    }
case FILTER_LP2:
    {
		float fxParamTmp = LP2OFFSET + params.effect.param1 + matrixFilterFrequency;
		fxParamTmp *= fxParamTmp;

		// Low pass... on the Frequency
		fxParam1 = (fxParamTmp + 9.0f * fxParam1) * .1f;

		const float fff = fastSin( sqrt3(fxParam1 * fxParam1 * 1.45f) );
		const float f = fabsf(fff);
    	const float pattern = (1 - fxParam2 * f * 0.997f);

    	float *sp = this->sampleBlock;
    	float localv0L = v0L;
    	float localv1L = v1L;
    	float localv0R = v0R;
    	float localv1R = v1R;

		float _ly1L = v2L, _ly1R = v2R;
		float _lx1L = v3L, _lx1R = v3R;
		const float f1 = clamp(0.517f - f * 0.151f, filterWindowMin, filterWindowMax);
		float coef1 = (1.0f - f1) / (1.0f + f1);

		float r = 0.993f;

    	for (int k=BLOCK_SIZE ; k--; ) {

			// Left voice
			*sp = _ly1L + ((-_ly1L + *sp) * r);

			localv0L = pattern * localv0L - f * sat25(localv1L + *sp);
			localv1L = pattern * localv1L + f * localv0L;

			localv0L = pattern * localv0L - f * (localv1L + *sp);
			localv1L = pattern * localv1L + f * localv0L;

			localv0L = pattern * localv0L - f * (localv1L + *sp);
			localv1L = pattern * localv1L + f * localv0L;

			_ly1L = coef1 * (_ly1L + localv1L) - _lx1L; // allpass
			_lx1L = localv1L;

			*sp++ = clamp(_ly1L * mixerGain, -ratioTimbres, ratioTimbres);

			// Right voice
			*sp = _ly1R + ((-_ly1R + *sp) * r);

			localv0R = pattern * localv0R - f * sat25(localv1R + *sp);
			localv1R = pattern * localv1R + f * localv0R;

			localv0R = pattern * localv0R - f * (localv1R + *sp);
			localv1R = pattern * localv1R + f * localv0R;

			localv0R = pattern * localv0R - f * (localv1R + *sp);
			localv1R = pattern * localv1R + f * localv0R;

			_ly1R = coef1 * (_ly1R + localv1R) - _lx1R; // allpass
			_lx1R = localv1R;

			*sp++ = clamp(_ly1R * mixerGain, -ratioTimbres, ratioTimbres);
		}
    	v0L = localv0L;
    	v1L = localv1L;
    	v0R = localv0R;
    	v1R = localv1R;

		v2L = _ly1L; v2R = _ly1R;
		v3L = _lx1L; v3R = _lx1R;
    }
    break;
case FILTER_HP2:
    {
		float fxParamTmp = LP2OFFSET + params.effect.param1 + matrixFilterFrequency;
		fxParamTmp *= fxParamTmp;

		// Low pass... on the Frequency
		fxParam1 = (fxParamTmp + 9.0f * fxParam1) * .1f;

		const float fff = fastSin( sqrt3(fxParam1 * fxParam1 * 1.45f) );
		const float f = fabsf(fff);
        const float pattern = (1 - fxParam2 * f);

        float *sp = this->sampleBlock;
        float localv0L = v0L;
        float localv1L = v1L;
        float localv0R = v0R;
        float localv1R = v1R;

        for (int k=0 ; k < BLOCK_SIZE ; k++) {

			// Left voice
			localv0L = pattern * localv0L + f * sat33(-localv1L + *sp);
			localv1L = pattern * localv1L + f * localv0L;

			localv0L = pattern * localv0L + f * (-localv1L + *sp);
			localv1L = pattern * localv1L + f * localv0L;

			localv0L = pattern * localv0L + f * (-localv1L + *sp);
			localv1L = pattern * localv1L + f * localv0L;

			*sp++ = clamp((*sp - localv1L) * mixerGain, -ratioTimbres, ratioTimbres);

			// Right voice
			localv0R = pattern * localv0R + f * sat33(-localv1R + *sp);
			localv1R = pattern * localv1R + f * localv0R;

			localv0R = pattern * localv0R + f * (-localv1R + *sp);
			localv1R = pattern * localv1R + f * localv0R;

			localv0R = pattern * localv0R + f * (-localv1R + *sp);
			localv1R = pattern * localv1R + f * localv0R;
			
			*sp++ = clamp((*sp - localv1R) * mixerGain, -ratioTimbres, ratioTimbres);
		}
        v0L = localv0L;
        v1L = localv1L;
        v0R = localv0R;
        v1R = localv1R;

    }
    break;
case FILTER_BP2:
{
    float fxParam1PlusMatrixTmp = clamp(params.effect.param1 + matrixFilterFrequency, 0, 1);
    if (fxParam1PlusMatrix != fxParam1PlusMatrixTmp) {
        fxParam1PlusMatrix = fxParam1PlusMatrixTmp;
        recomputeBPValues(params.effect.param2, fxParam1PlusMatrix * fxParam1PlusMatrix);
    }

    float localv0L = v0L;
    float localv0R = v0R;
    float localv1L = v1L;
    float localv1R = v1R;
    float *sp = this->sampleBlock;
    float in,temp,localV;

    for (int k=0 ; k < BLOCK_SIZE ; k++) {
		//Left
		in = fxParam1 * sat33(*sp);
		temp = in - fxParamA1 * localv0L - fxParamA2 * localv1L;
		localv1L = localv0L;
		localv0L = temp;
		localV = (temp + (in - fxParamA1 * localv0L - fxParamA2 * localv1L)) * 0.5f;
		*sp++ = clamp((localV + fxParamB2 * localv1L) * mixerGain, -ratioTimbres, ratioTimbres);

		localv1L = localv0L;
		localv0L = localV;

		//Right
		in = fxParam1 * sat33(*sp);
		temp = in - fxParamA1 * localv0R - fxParamA2 * localv1R;
		localv1R = localv0R;
		localv0R = temp;
		localV = (temp + (in - fxParamA1 * localv0R - fxParamA2 * localv1R)) * 0.5f;
		*sp++ = clamp((localV + fxParamB2 * localv1R) * mixerGain, -ratioTimbres, ratioTimbres);

		localv1R = localv0R;
		localv0R = localV;
	}

    v0L = localv0L;
    v0R = localv0R;
    v1L = localv1L;
    v1R = localv1R;

    break;
}
case FILTER_LP3:
{
	//https://www.musicdsp.org/en/latest/Filters/23-state-variable.html
	float fxParamTmp = SVFOFFSET + params.effect.param1 + matrixFilterFrequency;
	fxParamTmp *= fxParamTmp;
	// Low pass... on the Frequency
	fxParam1 = (fxParamTmp + 9.0f * fxParam1) * .1f;
	float fxParam1Clamped = clamp(fxParam1, 0, 1);

	float ramp1 = v8L;
	float b1inc = clamp(1.01f - sigmoidPos(foldPos(fxParam1 * fxParam1 * 0.01f) * fxParam1 * 0.0123f), 0.0001f, 1);
	float destL = v6L, destR = v6R;

	const float f = fxParam1Clamped * fxParam1Clamped * SVFRANGE;
	const float fb = sqrt3(1 - fxParam2 * 0.999f);
	const float scale = sqrt3(fb);

	float *sp = this->sampleBlock;
	float lowL = v0L, highL = 0, bandL = v1L;
	float lowR = v0R, highR = 0, bandR = v1R;

	const float svfGain = (1 + SVFGAINOFFSET + fxParam2 * fxParam2 * 0.75f) * mixerGain;

	float _ly1L = v2L, _ly1R = v2R;
	float _lx1L = v3L, _lx1R = v3R;
	const float f1 = clamp(0.33f + f * 0.43f, filterWindowMin, filterWindowMax);
	float coef1 = (1.0f - f1) / (1.0f + f1);

	for (int k = BLOCK_SIZE; k--;)	{
		// Left voice
		if (ramp1 >= 1)
		{
			destL = (*sp);
		}

		_ly1L = coef1 * (_ly1L + destL) - _lx1L; // allpass
		_lx1L = destL;

		lowL += f * bandL;
		bandL += f * (scale * _ly1L - lowL - fb * sat25(bandL));

		lowL += f * bandL;
		bandL += f * (scale * _ly1L - lowL - fb * (bandL));

		*sp++ = clamp(lowL * svfGain, -ratioTimbres, ratioTimbres);

		// Right voice

		if (ramp1 >= 1)
		{
			ramp1 -= 1;
			destR = (*sp);
		}

		_ly1R = coef1 * (_ly1R + destR) - _lx1R; // allpass
		_lx1R = destR;

		lowR += f * bandR;
		bandR += f * (scale * _ly1R - lowR - fb * sat25(bandR));

		lowR += f * bandR;
		bandR += f * (scale * _ly1R - lowR - fb * (bandR));

		*sp++ = clamp(lowR * svfGain, -ratioTimbres, ratioTimbres);

		ramp1 = clamp(ramp1 + b1inc, 0, 1);
	}

	v0L = lowL;
	v1L = bandL;
	v0R = lowR;
	v1R = bandR;

	v2L = _ly1L; v2R = _ly1R;
	v3L = _lx1L; v3R = _lx1R;

	v6L = destL;
	v6R = destR;
	v8L = ramp1;
}
break;
case FILTER_HP3: 
{
	//https://www.musicdsp.org/en/latest/Filters/23-state-variable.html
	float fxParamTmp = SVFOFFSET + params.effect.param1 + matrixFilterFrequency;
	fxParamTmp *= fxParamTmp;
	// Low pass... on the Frequency
	fxParam1 = clamp((fxParamTmp + 9.0f * fxParam1) * .1f, 0, 1);

	const float f = fxParam1 * fxParam1 * 0.93f;
	const float fb = sqrt3(1 - fxParam2 * 0.999f);
	const float scale = sqrt3(fb);

	float *sp = this->sampleBlock;
	float lowL = v0L, highL = 0, bandL = v1L;
	float lowR = v0R, highR = 0, bandR = v1R;

	const float svfGain = (1 + SVFGAINOFFSET + fxParam2 * fxParam2 * 0.75f) * mixerGain;

	float _ly1L = v2L, _ly1R = v2R;
	float _lx1L = v3L, _lx1R = v3R;
	const float f1 = clamp(0.15f + f * 0.33f, filterWindowMin, filterWindowMax);
	float coef1 = (1.0f - f1) / (1.0f + f1);

	for (int k=BLOCK_SIZE ; k--; ) {
		// Left voice
		_ly1L = coef1 * (_ly1L + *sp) - _lx1L; // allpass
		_lx1L = *sp;

		lowL = lowL + f * bandL;
		highL = scale * (_ly1L) - lowL - fb * sat33(bandL);
		bandL = f * highL + bandL;

		lowL = lowL + f * bandL;
		highL = scale * (_ly1L) - lowL - fb * bandL;
		bandL = f * highL + bandL;

		*sp++ = clamp(highL * svfGain, -ratioTimbres, ratioTimbres);

		// Right voice
		_ly1R = coef1 * (_ly1R + *sp) - _lx1R; // allpass
		_lx1R = *sp;

		lowR = lowR + f * bandR;
		highR = scale * (_ly1R) - lowR - fb * sat33(bandR);
		bandR = f * highR + bandR;

		lowR = lowR + f * bandR;
		highR = scale * (_ly1R) - lowR - fb * bandR;
		bandR = f * highR + bandR;
		
		*sp++ = clamp(highR * svfGain, -ratioTimbres, ratioTimbres);
	}

	v0L = lowL;
	v1L = bandL;
	v0R = lowR;
	v1R = bandR;

	v2L = _ly1L; v2R = _ly1R;
	v3L = _lx1L; v3R = _lx1R;
}
break;
case FILTER_BP3: 
{
	//https://www.musicdsp.org/en/latest/Filters/23-state-variable.html
	float fxParamTmp = SVFOFFSET + params.effect.param1 + matrixFilterFrequency;
	fxParamTmp *= fxParamTmp;
	// Low pass... on the Frequency
	fxParam1 = clamp((fxParamTmp + 9.0f * fxParam1) * .1f, 0, 1);

	const float f = fxParam1 * fxParam1 * SVFRANGE;
	const float fb = sqrt3(0.5f - fxParam2 * 0.495f);
	const float scale = sqrt3(fb);

	float *sp = this->sampleBlock;
	float lowL = v0L, highL = 0, bandL = v1L;
	float lowR = v0R, highR = 0, bandR = v1R;

	const float svfGain = (1 + SVFGAINOFFSET + fxParam2 * fxParam2 * 0.75f) * mixerGain;

	float _ly1L = v2L, _ly1R = v2R;
	float _lx1L = v3L, _lx1R = v3R;
	float _ly2L = v4L, _ly2R = v4R;
	float _lx2L = v5L, _lx2R = v5R;
	const float f1 = clamp(f * 0.56f , filterWindowMin, filterWindowMax);
	float coef1 = (1.0f - f1) / (1.0f + f1);
	const float f2 = clamp(0.25f + f * 0.08f , filterWindowMin, filterWindowMax);
	float coef2 = (1.0f - f1) / (1.0f + f1);

	for (int k=BLOCK_SIZE ; k--; ) {

		// Left voice
		_ly1L = coef1 * (_ly1L + *sp) - _lx1L; // allpass
		_lx1L = *sp;

		lowL = lowL + f * bandL;
		highL = scale * _ly1L - lowL - fb * sat25(bandL);
		bandL = f * highL + bandL;
		
		_ly2L = coef2 * (_ly2L + bandL) - _lx2L; // allpass 2
		_lx2L = bandL;

		*sp++ = clamp(_ly2L * svfGain, -ratioTimbres, ratioTimbres);

		// Right voice
		_ly1R = coef1 * (_ly1R + *sp) - _lx1R; // allpass
		_lx1R = *sp;

		lowR = lowR + f * bandR;
		highR = scale * _ly1R - lowR - fb * sat25(bandR);
		bandR = f * highR + bandR;

		_ly2R = coef2 * (_ly2R + bandR) - _lx2R; // allpass 2
		_lx2R = bandR;

		*sp++ = clamp(_ly2R * svfGain, -ratioTimbres, ratioTimbres);
	}

	v0L = lowL;
	v1L = bandL;
	v0R = lowR;
	v1R = bandR;

	v2L = _ly1L; v2R = _ly1R;
	v3L = _lx1L; v3R = _lx1R;
	v4L = _ly2L; v4R = _ly2R;
	v5L = _lx2L; v5R = _lx2R;

}
break;
case FILTER_PEAK:
{
	//https://www.musicdsp.org/en/latest/Filters/23-state-variable.html
	float fxParamTmp = SVFOFFSET + params.effect.param1 + matrixFilterFrequency;
	fxParamTmp *= fxParamTmp;
	// Low pass... on the Frequency
	fxParam1 = clamp((fxParamTmp + 9.0f * fxParam1) * .1f, 0, 1);

	const float f = fxParam1 * fxParam1 * SVFRANGE;
	const float fb = sqrt3(sqrt3(1 - fxParam2 * 0.999f));
	const float scale = sqrt3(fb);

	float *sp = this->sampleBlock;
	float lowL = v0L, highL = 0, bandL = v1L;
	float lowR = v0R, highR = 0, bandR = v1R;

	const float svfGain = (1 + SVFGAINOFFSET + fxParam2 * fxParam2 * 0.75f) * mixerGain;

	float _ly1L = v2L, _ly1R = v2R;
	float _lx1L = v3L, _lx1R = v3R;
	const float f1 = clamp(0.27f + f * 0.33f, filterWindowMin, filterWindowMax);
	float coef1 = (1.0f - f1) / (1.0f + f1);

	float out;

	for (int k=BLOCK_SIZE ; k--; ) {

		// Left voice
		lowL = lowL + f * bandL;
		highL = scale * (*sp) - lowL - fb * bandL;
		bandL = f * highL + bandL;

		lowL = lowL + f * bandL;
		highL = scale * (*sp) - lowL - fb * sat33(bandL);
		bandL = f * highL + bandL;

		out = (bandL + highL + lowL);

		_ly1L = coef1 * (_ly1L + out) - _lx1L; // allpass
		_lx1L = out;

		*sp++ = clamp(_ly1L * svfGain, -ratioTimbres, ratioTimbres);

		// Right voice
		lowR = lowR + f * bandR;
		highR = scale * (*sp) - lowR - fb * bandR;
		bandR = f * highR + bandR;

		lowR = lowR + f * bandR;
		highR = scale * (*sp) - lowR - fb * sat33(bandR);
		bandR = f * highR + bandR;

		out = (bandR + highR + lowR);

		_ly1R = coef1 * (_ly1R + out) - _lx1R; // allpass
		_lx1R = out;

		*sp++ = clamp(_ly1R * svfGain, -ratioTimbres, ratioTimbres);
	}

	v0L = lowL;
	v1L = bandL;
	v0R = lowR;
	v1R = bandR;

	v2L = _ly1L; v2R = _ly1R;
	v3L = _lx1L; v3R = _lx1R;
}
break;
case FILTER_NOTCH:
{
	//https://www.musicdsp.org/en/latest/Filters/23-state-variable.html
	float fxParamTmp = SVFOFFSET + params.effect.param1 + matrixFilterFrequency;
	fxParamTmp *= fxParamTmp;
	// Low pass... on the Frequency
	fxParam1 = clamp((fxParamTmp + 9.0f * fxParam1) * .1f, 0, 1);

	const float f = fxParam1 * fxParam1 * SVFRANGE;
	const float fb = sqrt3(1 - fxParam2 * 0.6f);
	const float scale = sqrt3(fb);

	float *sp = this->sampleBlock;
	float lowL = v0L, highL = 0, bandL = v1L;
	float lowR = v0R, highR = 0, bandR = v1R;
	float notch;

	const float svfGain = (1 + SVFGAINOFFSET) * mixerGain;

	float _ly1L = v2L, _ly1R = v2R;
	float _lx1L = v3L, _lx1R = v3R;
	const float f1 = clamp(fxParam1 * 0.66f , filterWindowMin, filterWindowMax);
	float coef1 = (1.0f - f1) / (1.0f + f1);

	for (int k=0 ; k < BLOCK_SIZE; k++) {

		// Left voice
		lowL = lowL + f * bandL;
		highL = scale * (*sp) - lowL - fb * bandL;
		bandL = f * highL + bandL;
		notch = (highL + lowL);

		_ly1L = coef1 * (_ly1L + notch) - _lx1L; // allpass
		_lx1L = notch;

		*sp++ = clamp(_ly1L * svfGain, -ratioTimbres, ratioTimbres);

		// Right voice
		lowR = lowR + f * bandR;
		highR = scale * (*sp) - lowR - fb * bandR;
		bandR = f * highR + bandR;
		notch = (highR + lowR);

		_ly1R = coef1 * (_ly1R + notch) - _lx1R; // allpass
		_lx1R = notch;

		*sp++ = clamp(_ly1R * svfGain, -ratioTimbres, ratioTimbres);
	}

	v0L = lowL;
	v1L = bandL;
	v0R = lowR;
	v1R = bandR;

	v2L = _ly1L; v2R = _ly1R;
	v3L = _lx1L; v3R = _lx1R;
}
break;
case FILTER_BELL:
{
	//filter algo from Andrew Simper
	//https://cytomic.com/files/dsp/SvfLinearTrapOptimised2.pdf
	float fxParamTmp = SVFOFFSET + params.effect.param1 + matrixFilterFrequency;
	fxParamTmp *= fxParamTmp;
	// Low pass... on the Frequency
	fxParam1 = clamp((fxParamTmp + 9.0f * fxParam1) * .1f, 0, 1);

	//A = 10 ^ (db / 40)
	const float A = (tanh3(fxParam2 * 2) * 1.5f) + 0.5f;

	const float res = 0.6f;
	const float k = 1 / (0.0001f + res * A);
	const float g = 0.0001f + (fxParam1);
	const float a1 = 1 / (1 + g * (g + k));
	const float a2 = g * a1;
	const float a3 = g * a2;
	const float amp = k * (A * A - 1);

	float *sp = this->sampleBlock;

	float ic1eqL = v0L, ic2eqL = v1L;
	float ic1eqR = v0R, ic2eqR = v1R;
	float v1, v2, v3, out;

	float _ly1L = v2L, _ly1R = v2R;
	float _lx1L = v3L, _lx1R = v3R;
	const float f1 = clamp(0.25f + fxParam1 * 0.33f , filterWindowMin, filterWindowMax);
	float coef1 = (1.0f - f1) / (1.0f + f1);

	for (int k=BLOCK_SIZE ; k--; ) {

		// Left voice
		v3 = (*sp) - ic2eqL;
		v1 = a1 * ic1eqL + a2 * v3;
		v2 = ic2eqL + a2 * ic1eqL + a3 * v3;
		ic1eqL = 2 * v1 - ic1eqL;
		ic2eqL = 2 * v2 - ic2eqL;
		
		_ly1L = coef1 * (_ly1L + v1) - _lx1L; // allpass
		_lx1L = v1;

		out = (*sp + (amp * _ly1L));

		*sp++ = clamp(out * mixerGain, -ratioTimbres, ratioTimbres);

		// Right voice
		v3 = (*sp) - ic2eqR;
		v1 = a1 * ic1eqR + a2 * v3;
		v2 = ic2eqR + a2 * ic1eqR + a3 * v3;
		ic1eqR = 2 * v1 - ic1eqR;
		ic2eqR = 2 * v2 - ic2eqR;

		_ly1R = coef1 * (_ly1R + v1) - _lx1R; // allpass
		_lx1R = v1;

		out = (*sp + (amp * _ly1R));

		*sp++ = clamp(out * mixerGain, -ratioTimbres, ratioTimbres);
	}

	v0L = ic1eqL;
	v1L = ic2eqL;
	v0R = ic1eqR;
	v1R = ic2eqR;

	v2L = _ly1L; v2R = _ly1R;
	v3L = _lx1L; v3R = _lx1R;
}
break;
case FILTER_LOWSHELF:
{
	//filter algo from Andrew Simper
	//https://cytomic.com/files/dsp/SvfLinearTrapOptimised2.pdf
	float fxParamTmp = SVFOFFSET + params.effect.param1 + matrixFilterFrequency;
	fxParamTmp *= fxParamTmp;
	// Low pass... on the Frequency
	fxParam1 = clamp((fxParamTmp + 9.0f * fxParam1) * .1f, 0, 1);

	//A = 10 ^ (db / 40)
	const float A = (tanh3(fxParam2 * 2) * 1) + 0.5f;

	const float res = 0.5f;
	const float k = 1 / (0.0001f + res);
	const float g = 0.0001f + (fxParam1);
	const float a1 = 1 / (1 + g * (g + k));
	const float a2 = g * a1;
	const float a3 = g * a2;
	const float m1 = k * (A - 1);
	const float m2 = (A * A - 1);

	float *sp = this->sampleBlock;

	float ic1eqL = v0L, ic2eqL = v1L;
	float ic1eqR = v0R, ic2eqR = v1R;
	float v1, v2, v3, out;

	const float svfGain = mixerGain * 0.8f;

	float _ly1L = v2L, _ly1R = v2R;
	float _lx1L = v3L, _lx1R = v3R;
	const float f1 = clamp(0.33f + fxParam1 * 0.33f , filterWindowMin, filterWindowMax);
	float coef1 = (1.0f - f1) / (1.0f + f1);

	for (int k=BLOCK_SIZE ; k--; ) {

		// Left voice
		v3 = (*sp) - ic2eqL;
		v1 = a1 * ic1eqL + a2 * v3;
		v2 = ic2eqL + a2 * ic1eqL + a3 * v3;
		ic1eqL = 2 * v1 - ic1eqL;
		ic2eqL = 2 * v2 - ic2eqL;
		out = (*sp + (m1 * v1 + m2 * v2));
		_ly1L = coef1 * (_ly1L + out) - _lx1L; // allpass
		_lx1L = out;

		*sp++ = clamp(_ly1L * svfGain, -ratioTimbres, ratioTimbres);

		// Right voice
		v3 = (*sp) - ic2eqR;
		v1 = a1 * ic1eqR + a2 * v3;
		v2 = ic2eqR + a2 * ic1eqR + a3 * v3;
		ic1eqR = 2 * v1 - ic1eqR;
		ic2eqR = 2 * v2 - ic2eqR;
		out = (*sp + (m1 * v1 + m2 * v2));

		_ly1R = coef1 * (_ly1R + out) - _lx1R; // allpass
		_lx1R = out;

		*sp++ = clamp(_ly1R * svfGain, -ratioTimbres, ratioTimbres);
	}

	v0L = ic1eqL;
	v1L = ic2eqL;
	v0R = ic1eqR;
	v1R = ic2eqR;

	v2L = _ly1L; v2R = _ly1R;
	v3L = _lx1L; v3R = _lx1R;
}
break;
case FILTER_HIGHSHELF:
{
	//filter algo from Andrew Simper
	//https://cytomic.com/files/dsp/SvfLinearTrapOptimised2.pdf
	float fxParamTmp = SVFOFFSET + params.effect.param1 + matrixFilterFrequency;
	fxParamTmp *= fxParamTmp;
	// Low pass... on the Frequency
	fxParam1 = clamp((fxParamTmp + 9.0f * fxParam1) * .1f, 0, 1);

	//A = 10 ^ (db / 40)
	const float A = (tanh3(fxParam2 * 2) * 1) + 0.5f;

	const float res = 0.5f;
	const float k = 1 / (0.0001f + res);
	const float g = 0.0001f + (fxParam1);
	const float a1 = 1 / (1 + g * (g + k));
	const float a2 = g * a1;
	const float a3 = g * a2;
	const float m0 = A * A;
	const float m1 = k * (A - 1) * A;
	const float m2 = (1 - A * A);

	float *sp = this->sampleBlock;

	float ic1eqL = v0L, ic2eqL = v1L;
	float ic1eqR = v0R, ic2eqR = v1R;
	float v1, v2, v3, out;

	const float svfGain = mixerGain * 0.8f;

	float _ly1L = v2L, _ly1R = v2R;
	float _lx1L = v3L, _lx1R = v3R;
	const float f1 = clamp(0.33f + fxParam1 * 0.33f , filterWindowMin, filterWindowMax);
	float coef1 = (1.0f - f1) / (1.0f + f1);

	for (int k=BLOCK_SIZE ; k--; ) {

		// Left voice
		v3 = (*sp) - ic2eqL;
		v1 = a1 * ic1eqL + a2 * v3;
		v2 = ic2eqL + a2 * ic1eqL + a3 * v3;
		ic1eqL = 2 * v1 - ic1eqL;
		ic2eqL = 2 * v2 - ic2eqL;
		
		out = (m0 * *sp + (m1 * v1 + m2 * v2));
		_ly1L = coef1 * (_ly1L + out) - _lx1L; // allpass
		_lx1L = out;

		*sp++ = clamp(_ly1L * svfGain, -ratioTimbres, ratioTimbres);

		// Right voice
		v3 = (*sp) - ic2eqR;
		v1 = a1 * ic1eqR + a2 * v3;
		v2 = ic2eqR + a2 * ic1eqR + a3 * v3;
		ic1eqR = 2 * v1 - ic1eqR;
		ic2eqR = 2 * v2 - ic2eqR;

		out = (m0 * *sp + (m1 * v1 + m2 * v2));
		_ly1R = coef1 * (_ly1R + out) - _lx1R; // allpass
		_lx1R = out;

		*sp++ = clamp(_ly1R * svfGain, -ratioTimbres, ratioTimbres);
	}

	v0L = ic1eqL;
	v1L = ic2eqL;
	v0R = ic1eqR;
	v1R = ic2eqR;

	v2L = _ly1L; v2R = _ly1R;
	v3L = _lx1L; v3R = _lx1R;
}
break;
case FILTER_LPHP:
{
	float fxParamTmp = params.effect.param1 + matrixFilterFrequency;
	fxParamTmp *= fxParamTmp;

	// Low pass... on the Frequency
	fxParam1 = clamp((fxParamTmp + 9.0f * fxParam1) * .1f, 0, 1);

	const int mixWet = (fxParam1 * 122);
	const float mixA = (1 + fxParam2 * 2) * panTable[122 - mixWet];
	const float mixB = 2.5f * panTable[5 + mixWet];

	const float f = fxParam1 * fxParam1 * 1.5f;
	const float pattern = (1 - fxParam2 * f);

	float *sp = this->sampleBlock;
	float localv0L = v0L;
	float localv1L = v1L;
	float localv0R = v0R;
	float localv1R = v1R;
	float out;

	float _ly1L = v2L, _ly1R = v2R;
	float _lx1L = v3L, _lx1R = v3R;

	const float f1 = clamp(0.27f + fxParam1 * 0.44f , filterWindowMin, filterWindowMax);
	float coef1 = (1.0f - f1) / (1.0f + f1);

	const float gain = mixerGain * 1.3f;

	for (int k = BLOCK_SIZE ; k--; ) {

		// Left voice

		_ly1L = coef1 * (_ly1L + (*sp)) - _lx1L; // allpass
		_lx1L = (*sp);

		localv0L = pattern * localv0L + (f * (-localv1L + _ly1L));
		localv1L = pattern * localv1L + f * localv0L;

		localv0L = pattern * localv0L + (f * (-localv1L + _ly1L));
		localv1L = pattern * localv1L + f * localv0L;

		out = sat33((localv1L * mixA) + ((_ly1L - localv1L) * mixB));

		*sp++ = clamp(out * gain, -ratioTimbres, ratioTimbres);

		// Right voice

		_ly1R = coef1 * (_ly1R + (*sp)) - _lx1R; // allpass
		_lx1R = (*sp);

		localv0R = pattern * localv0R + (f * (-localv1R + _ly1R));
		localv1R = pattern * localv1R + f * localv0R;
		
		localv0R = pattern * localv0R + (f * (-localv1R + _ly1R));
		localv1R = pattern * localv1R + f * localv0R;

		out = sat33((localv1R * mixA) + ((_ly1R - localv1R) * mixB));

		*sp++ = clamp(out * gain, -ratioTimbres, ratioTimbres);
	}
	v0L = localv0L;
	v1L = localv1L;
	v0R = localv0R;
	v1R = localv1R;

	v2L = _ly1L; v2R = _ly1R;
	v3L = _lx1L; v3R = _lx1R;
}
break;
case FILTER_BPds:
{
	float fxParamTmp = SVFOFFSET + params.effect.param1 + matrixFilterFrequency;
	fxParamTmp *= fxParamTmp;
	// Low pass... on the Frequency
	fxParam1 = clamp((fxParamTmp + 9.0f * fxParam1) * .1f, 0, 1);

	const float f = fxParam1 * fxParam1 * SVFRANGE;
	const float fb = sqrt3(0.5f - fxParam2 * 0.4995f);
	const float scale = sqrt3(fb);

	float *sp = this->sampleBlock;
	float lowL = v0L, highL = 0, bandL = v1L;
	float lowR = v0R, highR = 0, bandR = v1R;

	const float svfGain = (1 + SVFGAINOFFSET + fxParam2 * fxParam2 * 0.75f) * mixerGain;

	const float sat = 1 + fxParam2;

	float _ly1L = v2L, _ly1R = v2R;
	float _lx1L = v3L, _lx1R = v3R;
	const float f1 = clamp(fxParam1 * 0.35f , filterWindowMin, filterWindowMax);
	float coef1 = (1.0f - f1) / (1.0f + f1);
	float outL = 0, outR = 0;

	const float r = 0.9840f;

	for (int k=BLOCK_SIZE ; k--; ) {

		// Left voice
		*sp = outL + ((-outL + *sp) * r);

		lowL = lowL + f * bandL;
		highL = scale * (*sp) - lowL - fb * bandL;
		bandL = (f * highL) + bandL;
		_ly1L = coef1 * (_ly1L + bandL) - _lx1L; // allpass
		_lx1L = bandL;
		
		outL = sat25(_ly1L * sat);
		*sp++ = clamp( outL * svfGain, -ratioTimbres, ratioTimbres);

		// Right voice
		*sp = outR + ((-outR + *sp) * r);
		
		lowR = lowR + f * bandR;
		highR = scale * (*sp) - lowR - fb * bandR;
		bandR = (f * highR) + bandR;
		_ly1R = coef1 * (_ly1R + bandR) - _lx1R; // allpass
		_lx1R = bandR;

		outR = sat25(_ly1R * sat);
		*sp++ = clamp( outR * svfGain, -ratioTimbres, ratioTimbres);
	}

	v0L = lowL;
	v1L = bandL;
	v0R = lowR;
	v1R = bandR;

	v2L = _ly1L; v2R = _ly1R;
	v3L = _lx1L; v3R = _lx1R;
}
break;
case FILTER_LPWS:
	{
		float fxParamTmp = params.effect.param1 + matrixFilterFrequency;
		fxParamTmp *= fxParamTmp;

		// Low pass... on the Frequency
		fxParam1 = clamp((fxParamTmp + 9.0f * fxParam1) * .1f, 0, 1);

		const float a = 1.f - fxParam1;
		const float b = 1.f - a;

		float *sp = this->sampleBlock;
		float localv0L = v0L;
		float localv0R = v0R;

		const int mixWet = (params.effect.param2 * 127);
		const float mixA = panTable[mixWet] * mixerGain;
		const float mixB = panTable[127 - mixWet] * mixerGain;

		float _ly1L = v2L, _ly1R = v2R;
		float _lx1L = v3L, _lx1R = v3R;
		const float f1 = 0.27f + fxParam1 * 0.027;//clamp(fxParam1 - 0.26f , filterWindowMin, filterWindowMax);
		float coef1 = (1.0f - f1) / (1.0f + f1);

		for (int k=BLOCK_SIZE ; k--; ) {
			// Left voice
			localv0L = (*sp  * b) + (localv0L * a);

			_ly1L = coef1 * (_ly1L + localv0L) - _lx1L; // allpass
			_lx1L = localv0L;

			*sp++ = clamp((sigmoid(sat25(_ly1L * 2.0f)) * mixA + (mixB * (*sp))), -ratioTimbres, ratioTimbres);

			// Right voice
			localv0R = (*sp  * b) + (localv0R * a);

			_ly1R = coef1 * (_ly1R + localv0R) - _lx1R; // allpass
			_lx1R = localv0R;

			*sp++ = clamp((sigmoid(sat25(_ly1R * 2.0f)) * mixA + (mixB * (*sp))), -ratioTimbres, ratioTimbres);
		}
    	v0L = localv0L;
    	v0R = localv0R;

		v2L = _ly1L; v2R = _ly1R;
		v3L = _lx1L; v3R = _lx1R;
	}
	break;
case FILTER_TILT:
    {
		float fxParamTmp = params.effect.param1 + matrixFilterFrequency;
		fxParamTmp *= fxParamTmp;

		// Low pass... on the Frequency
		fxParam1 = clamp((fxParamTmp + 9.0f * fxParam1) * .1f, 0, 1);

		const float f1 = clamp(fxParam1 * 0.24f + 0.09f , filterWindowMin, filterWindowMax);
		float coef1 = (1.0f - f1) / (1.0f + f1);

		const float res = 0.85f;

		const float amp = 19.93f;
		const float gain = (params.effect.param2 - 0.5f);
		const float gfactor = 10;
		float g1, g2;
		if (gain > 0) {
			g1 = -gfactor * gain;
			g2 = gain;
		} else {
			g1 = -gain;
			g2 = gfactor * gain;
		};

		//two separate gains
		const float lgain = expf_fast(g1 / amp) - 1.f;
		const float hgain = expf_fast(g2 / amp) - 1.f;

		float *sp = this->sampleBlock;
		float localv0L = v0L;
		float localv0R = v0R;
		float localv1L = v1L;
		float localv1R = v1R;

		float _ly1L = v2L, _ly1R = v2R;
		float _ly2L = v3L, _ly2R = v3R;
		float _lx1L = v4L, _lx1R = v4R;

		float out;

		for (int k=BLOCK_SIZE ; k--; ) {
			// Left voice
			localv0L = res * localv0L - fxParam1 * localv1L + sigmoid(*sp);
			localv1L = res * localv1L + fxParam1 * localv0L;

			out = (*sp + lgain * localv1L + hgain * (*sp - localv1L));

			_ly1L = coef1 * (_ly1L + out) - _lx1L; // allpass
			_lx1L = out;

			*sp++ = clamp(_ly1L * mixerGain, -ratioTimbres, ratioTimbres);

			// Right voice
			localv0R = res * localv0R - fxParam1 * localv1R + sigmoid(*sp);
			localv1R = res * localv1R + fxParam1 * localv0R;

			out = (*sp + lgain * localv1R + hgain * (*sp - localv1R));

			_ly1R = coef1 * (_ly1R + out) - _lx1R; // allpass
			_lx1R = out;

			*sp++ = clamp(_ly1R * mixerGain, -ratioTimbres, ratioTimbres);
		}

        v0L = localv0L;
        v0R = localv0R;
        v1L = localv1L;
        v1R = localv1R;

		v2L = _ly1L; v2R = _ly1R;
		v3L = _ly2L; v3R = _ly2R;
		v4L = _lx1L; v4R = _lx1R;

    }
    break;
case FILTER_STEREO:
{
	float fxParamTmp = fabsf(params.effect.param1 + matrixFilterFrequency);
	fxParam1 = ((fxParamTmp + 19.0f * fxParam1) * .05f);

	float OffsetTmp = fabsf(params.effect.param2);
	fxParam2 = ((OffsetTmp + 19.0f * fxParam2) * .05f);

	const float offset = fxParam2 * 0.66f - 0.33f;

	const float f1 = clamp((fxParam1), 0.001f, 0.99f) * 1.8f - 0.9f;
	const float f2 = clamp((fxParam1 + offset), 0.001f, 0.99f) * 1.8f - 0.9f;
	const float f3 = clamp((fxParam1 + offset * 2), 0.001f, 0.99f) * 1.8f - 0.9f;;

	float *sp = this->sampleBlock;
	float lowL = v0L, highL = 0, bandL = v1L;
	float lowR = v0R, highR = 0, bandR = v1R;
	float lowL2 = v2L, highL2 = 0, bandL2 = v3L;
	float lowR2 = v2R, highR2 = 0, bandR2 = v3R;
	float lowL3 = v4L, highL3 = 0, bandL3 = v5L;
	float lowR3 = v4R, highR3 = 0, bandR3 = v5R;
	float out;

	for (int k = BLOCK_SIZE ; k--; ) {
		// Left voice
		
		lowL = (*sp) + f1 * (bandL = lowL - f1 * (*sp));
		highL = (bandL + (*sp)) * 0.5f;

		lowL2 = highL + f2 * (bandL2 = (lowL2) - f2 * lowL);
		highL2 = ((bandL2) + highL) * 0.5f;

		lowL3 = lowL2 + f3 * (bandL3 = lowL3 - f3 * lowL2);
		highL3 = (bandL3 + highL2) * 0.5f;

		*sp++ = clamp(highL3 * mixerGain, -ratioTimbres, ratioTimbres);

		// Right voice
		lowR = (*sp) + f1 * (bandR = lowR - f1 * (*sp));
		highR = (bandR + (*sp)) * 0.5f;

		lowR2 = lowR + f2 * (bandR2 = (lowR2) - f2 * lowR);
		highR2 = ((bandR2) + highR) * 0.5f;

		lowR3 = lowR2 + f3 * (bandR3 = lowR3 - f3 * lowR2);
		highR3 = (bandR3 + highR2) * 0.5f;

		*sp++ = clamp(highR3 * mixerGain, -ratioTimbres, ratioTimbres);
	}

	v0L = lowL;
	v1L = bandL;
	v0R = lowR;
	v1R = bandR;

	v2L = lowL2;
	v3L = bandL2;
	v2R = lowR2;
	v3R = bandR2;

	v4L = lowL3;
	v5L = bandL3;
	v4R = lowR3;
	v5R = bandR3;
}
break;
case FILTER_SAT:
	{
		float fxParamTmp = params.effect.param1 + matrixFilterFrequency;
		fxParamTmp *= fxParamTmp;

		// Low pass... on the Frequency
		fxParam1 = clamp((fxParamTmp + 9.0f * fxParam1) * .1f, 0, 1);

		const float f1 = clamp((fxParam1), 0.001f, 1); // allpass F
		float coef1 = (1.0f - f1) / (1.0f + f1);

		float *sp = this->sampleBlock;

		float localv0L = v0L;
		float localv0R = v0R;

		const float a = 0.95f - fxParam2 * 0.599999f;
		const float b = 1.f - a;

		const float threshold = (sqrt3(fxParam1) * 0.4f) * numberVoicesAttn;
		const float thresTop = (threshold + 1) * 0.5f;
		const float invT = 1.f / thresTop;

		for (int k=BLOCK_SIZE ; k--; ) {
			//LEFT
			localv0L = sigmoid(*sp);
			if(fabsf(localv0L) > threshold) {
				localv0L = localv0L > 1 ? thresTop : localv0L * invT;
			}
			localv0L = (*sp * b) + (localv0L * a);
			*sp++ = clamp((*sp - localv0L) * mixerGain, -ratioTimbres, ratioTimbres);

			//RIGHT
			localv0R = sigmoid(*sp);
			if(fabsf(localv0R) > threshold) {
				localv0R = localv0R > 1 ? thresTop : localv0R * invT;
			}
			localv0R = (*sp * b) + (localv0R * a);
			*sp++ = clamp((*sp - localv0R) * mixerGain, -ratioTimbres, ratioTimbres);
		}
    	v0L = localv0L;
    	v0R = localv0R;
	}
	break;
case FILTER_SIGMOID:
	{
		float fxParamTmp = params.effect.param1 + matrixFilterFrequency;
		fxParamTmp *= fxParamTmp;

		// Low pass... on the Frequency
		fxParam1 = clamp((fxParamTmp + 9.0f * fxParam1) * .1f, 0, 1);

		float *sp = this->sampleBlock;
		float localv0L = v0L;
		float localv1L = v1L;
		float localv0R = v0R;
		float localv1R = v1R;

		float f = fxParam2 * 0.5f + 0.12f;
		float pattern = (1 - 0.7f * f);
		float invAttn = sqrt3(numberOfVoiceInverse);
		int drive = clamp(27 + sqrt3(fxParam1) * 86, 0, 255);
		float gain = 1.1f + 44 * panTable[drive];
		float gainCorrection = (1.2f - sqrt3(panTable[64 + (drive >> 1)] * 0.6f));
		float bias = -0.1f + (fxParam1 * 0.2f);

		for (int k=BLOCK_SIZE ; k--; ) {
			// Left voice
			localv0L = tanh3(bias + sat33(*sp) * gain) * gainCorrection;
			localv0L = pattern * localv0L + f * (*sp - localv1L);
			localv1L = pattern * localv1L + f * localv0L;

			*sp++ = clamp((*sp - localv1L) * mixerGain, -ratioTimbres, ratioTimbres);

			// Right voice
			localv0R = tanh3(bias + sat33(*sp) * gain) * gainCorrection;
			localv0R = pattern * localv0R + f * (*sp - localv1R);
			localv1R = pattern * localv1R + f * localv0R;

			*sp++ = clamp((*sp - localv1R) * mixerGain, -ratioTimbres, ratioTimbres);
		}

    	v0L = localv0L;
    	v0R = localv0R;
        v1L = localv1L;
        v1R = localv1R;
	}
	break;
case FILTER_FOLD:
	{
		//https://www.desmos.com/calculator/ge2wvg2wgj

		float fxParamTmp = params.effect.param1 + matrixFilterFrequency;
		fxParamTmp *= fxParamTmp;

		// Low pass... on the Frequency
		fxParam1 = clamp((fxParamTmp + 9.0f * fxParam1) * .1f, 0, 1);

		float *sp = this->sampleBlock;
		float localv0L = v0L;
		float localv1L = v1L;
		float localv0R = v0R;
		float localv1R = v1R;

		float f = fxParam2;
		float f4 = f * 4;//optimisation
		float pattern = (1 - 0.6f * f);

		float drive = sqrt3(fxParam1);
		float gain = (1 + 52 * (drive)) * 0.25f;
		float finalGain = (1 - (drive / (drive + 0.05f)) * 0.7f) * mixerGain  * 0.95f;
	
		float _ly1L = v2L, _ly1R = v2R;
		float _lx1L = v3L, _lx1R = v3R;
		const float f1 = clamp(0.57f - fxParam1 * 0.43f, filterWindowMin, filterWindowMax);
		float coef1 = (1.0f - f1) / (1.0f + f1);

		for (int k=BLOCK_SIZE ; k--; ) {
			//LEFT
			_ly1L = coef1 * (_ly1L + *sp) - _lx1L; // allpass
			_lx1L = *sp;

			localv0L = pattern * localv0L - f * localv1L + f4 * fold(_ly1L * gain);
			localv1L = pattern * localv1L + f * localv0L;

			*sp++ = clamp(localv1L * finalGain, -ratioTimbres, ratioTimbres);

			//RIGHT
			_ly1R = coef1 * (_ly1R + *sp) - _lx1R; // allpass
			_lx1R = *sp;

			localv0R = pattern * localv0R - f * localv1R + f4 * fold(_ly1R * gain);
			localv1R = pattern * localv1R + f * localv0R;

			*sp++ = clamp(localv1R * finalGain, -ratioTimbres, ratioTimbres);
		}

        v0L = localv0L;
        v0R = localv0R;
        v1L = localv1L;
        v1R = localv1R;

		v2L = _ly1L; v2R = _ly1R;
		v3L = _lx1L; v3R = _lx1R;
	}
	break;
case FILTER_WRAP:
	{
		float fxParamTmp = params.effect.param1 + matrixFilterFrequency;
		fxParamTmp *= fxParamTmp;

		// Low pass... on the Frequency
		fxParam1 = clamp((fxParamTmp + 9.0f * fxParam1) * .1f, 0, 1);

		float *sp = this->sampleBlock;
		float localv0L = v0L;
		float localv1L = v1L;
		float localv0R = v0R;
		float localv1R = v1R;

		float f = fxParam2;
		float pattern = (1 - 0.6f * f);

		float drive = sqrt3(fxParam1);
		float gain = (1 + 4 * (drive));
		float finalGain = (1 - sqrt3(f * 0.5f) * 0.75f) * mixerGain * 0.85f;

		float _ly1L = v2L, _ly1R = v2R;
		float _lx1L = v3L, _lx1R = v3R;
		const float f1 = clamp(0.58f - fxParam1 * 0.43f, filterWindowMin, filterWindowMax);
		float coef1 = (1.0f - f1) / (1.0f + f1);

		for (int k=BLOCK_SIZE ; k--; ) {
			//LEFT
			localv0L = pattern * localv0L + f * (wrap(*sp * gain) - localv1L);
			localv1L = pattern * localv1L + f * localv0L;

			_ly1L = coef1 * (_ly1L + localv1L) - _lx1L; // allpass
			_lx1L = localv1L;
			*sp++ = clamp(_ly1L * finalGain, -ratioTimbres, ratioTimbres);

			//RIGHT
			localv0R = pattern * localv0R + f * (wrap(*sp * gain) - localv1R);
			localv1R = pattern * localv1R + f * localv0R;

			_ly1R = coef1 * (_ly1R + localv1R) - _lx1R; // allpass
			_lx1R = localv1R;
			*sp++ = clamp(_ly1R * finalGain, -ratioTimbres, ratioTimbres);
		}

        v0L = localv0L;
        v0R = localv0R;
        v1L = localv1L;
        v1R = localv1R;

		v2L = _ly1L; v2R = _ly1R;
		v3L = _lx1L; v3R = _lx1R;
	}
	break;
case FILTER_ROT:
	{
		float fxParamTmp = params.effect.param1 + matrixFilterFrequency;
		fxParamTmp *= fxParamTmp;

		// Low pass... on the Frequency
		fxParam1 = (fxParamTmp + 199.0f * fxParam1) * .005f;

		float *sp = this->sampleBlock;
		float sahL = v5L, sahR = v5R;
		float destL = v6L, destR = v6R;
		float ramp1 = v0L;
		float b1S;
		float b1inc = 0.0125f + fxParam2 * fxParam2 * fxParam2 * 0.55f;

		const float fold1 = foldPos(fxParam1);
		const float f1 = clamp((0.58f - fold1 * 0.43f), filterWindowMin, filterWindowMax);
		float coef1 = (1.0f - f1) / (1.0f + f1);

		float _ly1L = v2L, _ly1R = v2R;
		float _lx1L = v3L, _lx1R = v3R;

		const float fold2 = foldPos(fxParam1 * 1.2f);
		const float f2 = clamp((0.33f + fold2 * 0.5f), filterWindowMin, filterWindowMax);
		float coef2 = (1.0f - f2) / (1.0f + f2);

		float _ly2L = v1L, _ly2R = v1R;
		float _lx2L = v4L, _lx2R = v4R;

		float angle = foldPos(fxParam1);
		// https://www.musicdsp.org/en/latest/Effects/255-stereo-field-rotation-via-transformation-matrix.html
		float cos_coef = fastSin(angle + 0.75f);
		float sin_coef = fastSin(angle);

		float outL, outR;

		for (int k=BLOCK_SIZE ; k--; ) {
			b1S = clamp(sigmoid(ramp1), 0, 1);
			// Left
			_ly1L = coef1 * (_ly1L + *sp) - _lx1L; // allpass
			_lx1L = *sp;

			if (ramp1 >= 1) {
				sahL = destL = _ly1L;
			} else {
				sahL = destL * (1 - b1S) + _ly1L * b1S;
			}
			
			_ly2L = coef2 * (_ly2L + sahL) - _lx2L; // allpass
			_lx2L = sahL;

			outL  = _ly2L * cos_coef - _ly2R * sin_coef;

			*sp++ = clamp(outL * mixerGain, -ratioTimbres, ratioTimbres);

			// Right
			_ly1R = coef1 * (_ly1R + *sp) - _lx1R; // allpass
			_lx1R = *sp;

			if (ramp1 >= 1)	{
				ramp1 -= 1;
				sahR = destR = _ly1R;
			} else {
				sahR = destR * (1 - b1S) + _ly1R * b1S;
			}

			_ly2R = coef2 * (_ly2R + sahR) - _lx2R; // allpass
			_lx2R = sahR;

			outR  = _ly2L * sin_coef + _ly2R * cos_coef;

			*sp++ = clamp(outR * mixerGain, -ratioTimbres, ratioTimbres);

			ramp1 += b1inc;
		}

		v0L = ramp1;
		v1L = _ly2L; v1R = _ly2R;
		v2L = _ly1L; v2R = _ly1R;
		v3L = _lx1L; v3R = _lx1R;
		v4L = _lx2L; v4R = _lx2R;
		v5L = sahL;  v5R = sahR;
		v6L = destL; v6R = destR;
	}
	break;
case FILTER_TEXTURE1:
	{
		float fxParamTmp = (params.effect.param1 + matrixFilterFrequency);
		fxParamTmp *= fxParamTmp;

		const uint_fast8_t random = (*(uint_fast8_t *)noise) & 0xff;
		if (random > 252) {
			fxParam1 += ((random & 1) * 0.007874015748031f);
		}

		// Low pass... on the Frequency
		fxParam1 = (fxParamTmp + 9.0f * fxParam1) * .1f;
		float p1Sin = fabsf(fastSin(fxParam1 * 1.57079f));

		float *sp = this->sampleBlock;
		float lowL = v0L, highL = 0, bandL = v1L;
		float lowR = v0R, highR = 0, bandR = v1R;
		float destL = v7L, destR = v7R;
		float out;

		float localInR = *sp, localInL = *sp;
		float localLowR = v1L, localLowL = v1R;

		float ramp1 = v8L;
		float b1inc = 0.025f + p1Sin * p1Sin;
		float b1S;

		float ramp2 = v8R;
		float b2inc = clamp(0.0125f + fxParam2 * fxParam2 * 0.55f + b1inc * 0.05f, 0, 1);
		float b2S;
		float targetLowL = v6L, targetLowR = v6R;

		const float f = (p1Sin * p1Sin * p1Sin) * 0.55f;
		const float fb = 0.97f - p1Sin * 0.05f;
		const float scale = sqrt3(fb);

		float _ly1L = v2L, _ly1R = v2R;
		float _lx1L = v3L, _lx1R = v3R;
		float _ly2L = v4L, _ly2R = v4R;
		float _lx2L = v5L, _lx2R = v5R;
		const float fold1 = foldPos(fxParam2);
		const float f1 = clamp(0.57f - fold1 * 0.33f, filterWindowMin, filterWindowMax);
		float coef1 = (1.0f - f1) / (1.0f + f1);
		const float f2 = clamp(0.50f - fold1 * 0.39f , filterWindowMin, filterWindowMax);
		float coef2 = (1.0f - f1) / (1.0f + f1);

		const float r = 0.9850f;

		for (int k=BLOCK_SIZE ; k--; ) {
			b1S = sigmoid(ramp1);
			b2S = sigmoid(ramp2);
			//LEFT
			*sp = _ly2L + ((-_ly2L + *sp) * r);
			if (ramp1 >= 1) {
				localInL = destL = *sp;
			} else {
				localInL = destL * (1 - b1S) + *sp * b1S;
			}

			if (ramp2 >= 1) {
				localLowL = targetLowL = sat33(localInL);
			} else {
				localLowL = targetLowL * (1 - b2S) + lowL * b2S;
			}

			_ly1L = coef1 * (_ly2L + localInL) - _lx1L; // allpass
			_lx1L = localInL;

			_ly2L = coef2 * (_ly2L + _ly1L) - _lx2L; // allpass 2
			_lx2L = _ly1L;

			lowL = localLowL + f * bandL;
			highL = scale * _ly1L - localLowL - fb * bandL;
			bandL = f * highL + bandL;
			out = localLowL + bandL + highL;

			*sp++ = clamp(out * mixerGain, -ratioTimbres, ratioTimbres);

			//RIGHT
			*sp = _ly2R + ((-_ly2R + *sp) * r);

			if (ramp1 >= 1)	{
				ramp1 -= 1;
				localInR = destR = *sp;
			} else {
				localInR = destR * (1 - b1S) + *sp * b1S;
			}

			if (ramp2 >= 1) {
				ramp2 -= 1;
				localLowR = targetLowR = sat33(localInR);
			} else {
				localLowR = targetLowR * (1 - b2S) + lowR * b2S;
			}

			_ly1R = coef1 * (_ly2R + localInR) - _lx1R; // allpass
			_lx1R = localInR;

			_ly2R = coef2 * (_ly2R + _ly1R) - _lx2R; // allpass 2
			_lx2R = _ly1R;

			lowR = localLowR + f * bandR;
			highR = scale * _ly1R - localLowR - fb * bandR;
			bandR = f * highR + bandR;
			out = localLowR + bandR + highR;

			*sp++ = clamp(out * mixerGain, -ratioTimbres, ratioTimbres);

			ramp1 += b1inc;
			ramp2 += b2inc;
		}

		v0L = lowL;
		v1L = bandL;
		v0R = lowR;
		v1R = bandR;

		v2L = _ly1L; v2R = _ly1R;
		v3L = _lx1L; v3R = _lx1R;
		v4L = _ly2L; v4R = _ly2R;
		v5L = _lx2L; v5R = _lx2R;

		v6L = targetLowL;
		v6R = targetLowR;

		v8L = ramp1;
		v8R = ramp2;
		v7L = destL;
		v7R = destR;
	}
    break;
case FILTER_TEXTURE2:
    {
		float fxParamTmp = (params.effect.param1 + matrixFilterFrequency);
		fxParamTmp *= fxParamTmp;

		const uint_fast8_t random = (*(uint_fast8_t *)noise) & 0xff;
		if (random > 252) {
			fxParam1 += ((random & 1) * 0.007874015748031f);
		}

		// Low pass... on the Frequency
		fxParam1 = (fxParamTmp + 9.0f * fxParam1) * .1f;
		float p1Sin = fabsf(fastSin(fxParam1 * 1.57079f));

		float *sp = this->sampleBlock;
		float lowL = v0L, highL = 0, bandL = v1L;
		float lowR = v0R, highR = 0, bandR = v1R;
		float destL = v7L, destR = v7R;
		float notch;

		float localInR = *sp, localInL = *sp;
		float localLowR = v1L, localLowL = v1R;

		float ramp1 = v8L;
		float b1inc = 0.125f + p1Sin * p1Sin * p1Sin;
		float b1S;

		float ramp2 = v8R;
		float b2inc = clamp(0.0125f + fxParam2 * fxParam2 * fxParam2 * 0.55f + b1inc * 0.05f, 0, 1);
		float b2S;
		float targetLowL = v6L, targetLowR = v6R;

		const float f = (p1Sin * p1Sin * p1Sin) * 0.5f;
		const float fb = 0.97f - p1Sin * 0.05f;
		const float scale = sqrt3(fb);

		float _ly1L = v2L, _ly1R = v2R;
		float _lx1L = v3L, _lx1R = v3R;
		float _ly2L = v4L, _ly2R = v4R;
		float _lx2L = v5L, _lx2R = v5R;
		const float f1 = clamp(0.57f - p1Sin * 0.33f, filterWindowMin, filterWindowMax);
		float coef1 = (1.0f - f1) / (1.0f + f1);
		const float f2 = clamp(0.50f - p1Sin * 0.39f , filterWindowMin, filterWindowMax);
		float coef2 = (1.0f - f1) / (1.0f + f1);

		const float r = 0.9850f;

		for (int k=BLOCK_SIZE ; k--; ) {
			b1S = sigmoid(ramp1);
			b2S = sigmoid(ramp2);
			//LEFT
			*sp = _ly2L + ((-_ly2L + *sp) * r);
			if (ramp1 >= 1) {
				localInL = destL = *sp;
			} else {
				localInL = destL * (1 - b1S) + *sp * b1S;
			}

			if (ramp2 >= 1) {
				localLowL = targetLowL = sat66(lowL);
			} else {
				localLowL = targetLowL * (1 - b2S) + lowL * b2S;
			}

			lowL = localLowL + f * bandL;
			highL = scale * localInL - localLowL - fb * bandL;
			bandL = f * highL + bandL;
			notch = localLowL + highL;

			_ly1L = coef1 * (_ly1L + notch) - _lx1L; // allpass
			_lx1L = notch;

			_ly2L = coef2 * (_ly2L + _ly1L) - _lx2L; // allpass 2
			_lx2L = _ly1L;

			*sp++ = clamp(_ly2L * mixerGain, -ratioTimbres, ratioTimbres);

			//RIGHT
			*sp = _ly2R + ((-_ly2R + *sp) * r);

			if (ramp1 >= 1)	{
				ramp1 -= 1;
				localInR = destR = *sp;
			} else {
				localInR = destR * (1 - b1S) + *sp * b1S;
			}

			if (ramp2 >= 1) {
				ramp2 -= 1;
				localLowR = targetLowR = sat66(lowR);
			} else {
				localLowR = targetLowR * (1 - b2S) + lowR * b2S;
			}

			lowR = localLowR + f * bandR;
			highR = scale * localInR - localLowR - fb * bandR;
			bandR = f * highR + bandR;
			notch = localLowR + highR;

			_ly1R = coef1 * (_ly1R + notch) - _lx1R; // allpass
			_lx1R = notch;

			_ly2R = coef2 * (_ly2R + _ly1R) - _lx2R; // allpass 2
			_lx2R = _ly1R;

			*sp++ = clamp(_ly2R * mixerGain, -ratioTimbres, ratioTimbres);

			ramp1 += b1inc;
			ramp2 += b2inc;
		}

		v0L = lowL;
		v1L = bandL;
		v0R = lowR;
		v1R = bandR;

		v2L = _ly1L; v2R = _ly1R;
		v3L = _lx1L; v3R = _lx1R;
		v4L = _ly2L; v4R = _ly2R;
		v5L = _lx2L; v5R = _lx2R;

		v6L = targetLowL;
		v6R = targetLowR;

		v8L = ramp1;
		v8R = ramp2;
		v7L = destL;
		v7R = destR;
    }
    break;
case FILTER_LPXOR:
	{
		float fxParamTmp = params.effect.param1 + matrixFilterFrequency;
		fxParamTmp *= fxParamTmp;

		const uint_fast8_t random = (*(uint_fast8_t *)noise) & 0xff;
		if (random > 252) {
			fxParam1 += ((random & 1) * 0.007874015748031f);
		}

		// Low pass... on the Frequency
		fxParam1 = (fxParamTmp + 9.0f * fxParam1) * .1f;
		float p1Sin = fabsf(fastSin(fxParam1 * 1.57079f));

		const float a = 1.f - p1Sin;
		const float a2f = a * SHORT2FLOAT;
		const float b = 1.f - a;

		float *sp = this->sampleBlock;
		float localv0L = v0L;
		float localv0R = v0R;
		float digitized;

		float ramp1 = v8L;
		float b1inc = 0.125f + ((p1Sin > 0.5f) ? (p1Sin * p1Sin * p1Sin ) : (1 - p1Sin) ) * 0.75f;
		float b1S;

		float localInR = *sp, localInL = *sp;
		float localLowR = v1L, localLowL = v1R;
		float destL = v7L, destR = v7R;

		float drive = (fxParam2 * fxParam2);
		float gain = (0.75f + 0.5f * drive);

		int digitsAL, digitsBL, digitsAR, digitsBR;
		digitsAL = digitsBL = digitsAR = digitsBR = 0;

		const short bitmask = 0x34;

		float _ly1L = v2L, _ly1R = v2R;
		float _lx1L = v3L, _lx1R = v3R;
		const float f1 = clamp(0.27f + p1Sin * 0.2f, filterWindowMin, filterWindowMax);
		float coef1 = (1.0f - f1) / (1.0f + f1);

		const float r = 0.980f;

		for (int k = BLOCK_SIZE; k--;) {
			// Left voice
			*sp = _ly1L + ((-_ly1L + *sp) * r);

			if (ramp1 >= 1) {
				localInL = destL = localv0L;
			} else {
				localInL = destL * (1 - b1S) + localv0L * b1S;
			}

			digitsAL = FLOAT2SHORT * fold(localInL * gain);
			digitsBL = FLOAT2SHORT * *sp;
			digitized = (float)(digitsAL ^ (digitsBL & bitmask));
			localv0L = (*sp * b) + (digitized * a2f);

			_ly1L = coef1 * (_ly1L + localv0L) - _lx1L; // allpass
			_lx1L = localv0L;

			*sp++ = clamp(_ly1L * mixerGain, -ratioTimbres, ratioTimbres);

			// Right voice
			*sp = _ly1R + ((-_ly1R + *sp) * r);

			if (ramp1 >= 1)	{
				ramp1 -= 1;
				localInR = destR = localv0R;
			} else {
				localInR = destR * (1 - b1S) + localv0R * b1S;
			}

			digitsAR = FLOAT2SHORT * fold(localInR * gain);
			digitsBR = FLOAT2SHORT * *sp;
			digitized = (float)(digitsAR ^ (digitsBR & bitmask));
			localv0R = (*sp * b) + (digitized * a2f);

			_ly1R = coef1 * (_ly1R + localv0R) - _lx1R; // allpass
			_lx1R = localv0R;

			*sp++ = clamp(_ly1R * mixerGain, -ratioTimbres, ratioTimbres);

			ramp1 += b1inc;
		}
    	v0L = localv0L;
    	v0R = localv0R;

		v2L = _ly1L; v2R = _ly1R;
		v3L = _lx1L; v3R = _lx1R;

		v8L = ramp1;
		v7L = destL;
		v7R = destR;
	}
	break;
case FILTER_LPXOR2:
	{
		float fxParamTmp = params.effect.param1 + matrixFilterFrequency;
		fxParamTmp *= fxParamTmp;

		const uint8_t random = (*(uint8_t *)noise) & 0xff;
		if (random > 252) {
			fxParam1 += ((random & 1) * 0.007874015748031f);
		}

		// Low pass... on the Frequency
		fxParam1 = ((fxParamTmp + 9.0f * fxParam1) * .1f);
		float p1Sin = fabsf(fastSin(fxParam1 * 1.57079f));

		const float a = 1.f - p1Sin;
		const float a2f = a * SHORT2FLOAT;
		const float b = 1.f - a;

		float *sp = this->sampleBlock;
		float localv0L = v0L;
		float localv0R = v0R;
		float digitized;

		float ramp1 = v8L;
		float b1inc = 0.125f + (1 - fxParam2 * fxParam2 * fxParam2) * 0.77f;
		float b1S;

		float localInR = *sp, localInL = *sp;
		float localLowR = v1L, localLowL = v1R;
		float destL = v7L, destR = v7R;

		float drive = (fxParam2 * fxParam2);
		float gain = (1 + 8 * (drive)) * 0.25f;

		int digitsAL, digitsBL, digitsAR, digitsBR;
		digitsAL = digitsBL = digitsAR = digitsBR = 0;

		const short bitmask = 0x9a - (int)(fxParam1 * 7);

		float _ly1L = v2L, _ly1R = v2R;
		float _lx1L = v3L, _lx1R = v3R;
		const float f1 = clamp(0.27f + p1Sin * 0.2f, filterWindowMin, filterWindowMax);
		float coef1 = (1.0f - f1) / (1.0f + f1);

		const float r = 0.9830f;

		for (int k=BLOCK_SIZE ; k--; ) {
			// Left voice
			*sp = _ly1L + ((-_ly1L + *sp) * r);

			if (ramp1 >= 1) {
				localInL = destL = *sp;
			} else {
				localInL = destL * (1 - b1S) + *sp * b1S;
			}

			digitsAL = FLOAT2SHORT * localv0L;
			digitsBL = FLOAT2SHORT * fold(*sp * gain);
			digitized = ((digitsAL | (digitsBL & bitmask)));
			localv0L = (localInL * b) + (digitized * a2f);

			_ly1L = coef1 * (_ly1L + localv0L) - _lx1L; // allpass
			_lx1L = localv0L;

			*sp++ = clamp(_ly1L * mixerGain, -ratioTimbres, ratioTimbres);

			// Right voice
			*sp = _ly1R + ((-_ly1R + *sp) * r);

			if (ramp1 >= 1)	{
				ramp1 -= 1;
				localInR = destR = *sp;
			} else {
				localInR = destR * (1 - b1S) + *sp * b1S;
			}

			digitsAR = FLOAT2SHORT * localv0R;
			digitsBR = FLOAT2SHORT * fold(*sp * gain);
			digitized = ((digitsAR | (digitsBR & bitmask)));
			localv0R = (localInR * b) + (digitized * a2f);

			_ly1R = coef1 * (_ly1R + localv0R) - _lx1R; // allpass
			_lx1R = localv0R;

			*sp++ = clamp(_ly1R * mixerGain, -ratioTimbres, ratioTimbres);

			ramp1 += b1inc;
		}
    	v0L = localv0L;
    	v0R = localv0R;

		v2L = _ly1L; v2R = _ly1R;
		v3L = _lx1L; v3R = _lx1R;

		v8L = ramp1;
		v7L = destL;
		v7R = destR;
	}
	break;
case FILTER_LPSIN:
    {
	float fxParamTmp = SVFOFFSET + params.effect.param1 + matrixFilterFrequency;
	fxParamTmp *= fxParamTmp;
	// Low pass... on the Frequency
	fxParam1 = clamp((fxParamTmp + 9.0f * fxParam1) * .1f, 0, 1);

	const float f = fxParam2 * fxParam2 * fxParam2;
	const float fb = 0.45f;
	const float scale = sqrt3(fb);
	const int pos = (int)(fxParam1 * 2060);

	float *sp = this->sampleBlock;
	float lowL = v0L, highL = 0, bandL = v1L;
	float lowR = v0R, highR = 0, bandR = v1R;

	const float svfGain = (1 + SVFGAINOFFSET + fxParam2 * fxParam2 * 0.75f) * mixerGain;
	float drive = fxParam1 * fxParam1 * 0.25f;
	
	for (int k = BLOCK_SIZE ; k--; ) {
		// Left voice
		*sp = lowL + ((-lowL + *sp) * 0.9840f);

		lowL = lowL + f * bandL;
		highL = scale * satSin(*sp, drive, pos) - lowL - fb * bandL;
		bandL = f * highL + bandL;

		*sp++ = clamp( lowL * svfGain, -ratioTimbres, ratioTimbres);

		// Right voice
		*sp = lowR + ((-lowR + *sp) * 0.9840f);

		lowR = lowR + f * bandR;
		highR = scale * satSin(*sp, drive, pos) - lowR - fb * bandR;
		bandR = f * highR + bandR;

		*sp++ = clamp( lowR * svfGain, -ratioTimbres, ratioTimbres);
	}

	v0L = lowL;
	v1L = bandL;
	v0R = lowR;
	v1R = bandR;
    }
    break;
case FILTER_HPSIN:
    {
	float fxParamTmp = SVFOFFSET + params.effect.param1 + matrixFilterFrequency;
	fxParamTmp *= fxParamTmp;
	// Low pass... on the Frequency
	fxParam1 = clamp((fxParamTmp + 9.0f * fxParam1) * .1f, 0, 1);

	const float f = fxParam2 * fxParam2 * fxParam2;
	const float fb = 0.94f;
	const float scale = sqrt3(fb);
	const int pos = (int)(fxParam1 * 2060);

	float *sp = this->sampleBlock;
	float lowL = v0L, highL = 0, bandL = v1L;
	float lowR = v0R, highR = 0, bandR = v1R;

	const float svfGain = (1 + SVFGAINOFFSET + fxParam2 * fxParam2 * 0.75f) * mixerGain;
	float drive = fxParam1 * fxParam1 * 0.25f;
	
	for (int k = BLOCK_SIZE ; k--; ) {
		// Left voice
		*sp = highL + ((-highL + *sp) * 0.9840f);

		lowL = lowL + f * bandL;
		highL = scale * satSin(*sp, drive, pos) - lowL - fb * bandL;
		bandL = f * highL + bandL;

		*sp++ = clamp( highL * svfGain, -ratioTimbres, ratioTimbres);

		// Right voice
		*sp = highR + ((-highR + *sp) * 0.9840f);

		lowR = lowR + f * bandR;
		highR = scale * satSin(*sp, drive, pos) - lowR - fb * bandR;
		bandR = f * highR + bandR;

		*sp++ = clamp( highR * svfGain, -ratioTimbres, ratioTimbres);
	}

	v0L = lowL;
	v1L = bandL;
	v0R = lowR;
	v1R = bandR;
    }
    break;
case FILTER_QUADNOTCH:
{
	//https://www.musicdsp.org/en/latest/Filters/23-state-variable.html
	float fxParamTmp = (params.effect.param1 + matrixFilterFrequency);
	fxParamTmp *= fxParamTmp;

	const float bipolarf = (fxParam1 - 0.5f);
	const float folded = fold(sigmoid(bipolarf * 13 * fxParam2)) * 4; // - < folded < 1
	const float folded2 = fold(fxParam1);

	fxParam1 = ((fxParamTmp + 9.0f * fxParam1) * .1f);
	
	float OffsetTmp = fabsf(params.effect.param2);
	fxParam2 = ((OffsetTmp + 9.0f * fxParam2) * .1f);

	const float offset = fxParam2 * fxParam2 * 0.17f;
	const float spread = 0.8f + fxParam2 * 0.8f;
	const float lrDelta = 0.0025f * folded;
	const float range = 0.47f;
	const float range2 = 0.51f;

	const float windowMin = 0.005f, windowMax = 0.99f;

	const float f1L = clamp(((folded2 - offset - lrDelta) * range) * 2, windowMin, windowMax);
	const float f2L = clamp(((folded2 + offset + lrDelta) * range2) * 2, windowMin, windowMax);
	const float f3L = clamp(((folded2 - (offset * 2) - lrDelta) * range2) * 2, windowMin, 1);
	const float f4L = clamp(((folded2 + (offset * 2) + lrDelta) * range) * 2, windowMin, 1);	
	const float f1R = clamp(((f1L - lrDelta) * range) * 2, windowMin, windowMax);
	const float f2R = clamp(((f2L + lrDelta) * range2) * 2, windowMin, windowMax);
	const float f3R = clamp(((f3L - lrDelta) * range2) * 2, windowMin, windowMax);
	const float f4R = clamp(((f3L + lrDelta) * range) * 2, windowMin, windowMax);

	float *sp = this->sampleBlock;
	float lowL = v0L, highL = 0, bandL = v1L;
	float lowR = v0R, highR = 0, bandR = v1R;
	float lowL2 = v2L, highL2 = 0, bandL2 = v3L;
	float lowR2 = v2R, highR2 = 0, bandR2 = v3R;
	float lowL3 = v4L, highL3 = 0, bandL3 = v5L;
	float lowR3 = v4R, highR3 = 0, bandR3 = v5R;
	float lowL4 = v6L, highL4 = 0, bandL4 = v7L;
	float lowR4 = v6R, highR4 = 0, bandR4 = v7R;

	for (int k = BLOCK_SIZE ; k--; ) {
		// Left voice
		*sp = (highL4 + lowL4) + ((-(highL4 + lowL4) + *sp) * 0.9840f);

		lowL = lowL + f1L * bandL;
		highL = (*sp) - lowL - bandL;
		bandL = f1L * highL + bandL;

		lowL2 = lowL2 + f2L * bandL2;
		highL2 = (highL + lowL) - lowL2 - bandL2;
		bandL2 = f2L * (highL2) + bandL2;

		lowL3 = lowL3 + f3L * bandL3;
		highL3 = (highL2 + lowL2) - lowL3 - bandL3;
		bandL3 = f3L * highL3 + bandL3;

		lowL4 = lowL4 + f4L * bandL4;
		highL4 = (highL3 + lowL3) - lowL4 - bandL4;
		bandL4 = f4L * highL4 + bandL4;

		*sp++ = clamp((highL4 + lowL4) * mixerGain, -ratioTimbres, ratioTimbres);

		// Right voice
		*sp = (highR4 + lowR4) + ((-(highR4 + lowR4) + *sp) * 0.9840f);

		lowR = lowR + f1R * bandR;
		highR = (*sp) - lowR - bandR;
		bandR = f1R * highR + bandR;

		lowR2 = lowR2 + f2R * bandR2;
		highR2 = (highR + lowR) - lowR2 - bandR2;
		bandR2 = f2R * (highR2) + bandR2;

		lowR3 = lowR3 + f3R * bandR3;
		highR3 = (highR2 + lowR2) - lowR3 - bandR3;
		bandR3 = f3R * highR3 + bandR3;

		lowR4 = lowR4 + f4R * bandR4;
		highR4 = (highR3 + lowR3) - lowR4 - bandR4;
		bandR4 = f4R * highR4 + bandR4;

		*sp++ = clamp((highR4 + lowR4) * mixerGain, -ratioTimbres, ratioTimbres);
	}

	v0L = lowL;
	v1L = bandL;
	v0R = lowR;
	v1R = bandR;

	v2L = lowL2;
	v3L = bandL2;
	v2R = lowR2;
	v3R = bandR2;

	v4L = lowL3;
	v5L = bandL3;
	v4R = lowR3;
	v5R = bandR3;

	v6L = lowL4;
	v7L = bandL4;
	v6R = lowR4;
	v7R = bandR4;
}
break;
case FILTER_AP4 :
{
	//http://denniscronin.net/dsp/vst.html
	float fxParamTmp = (params.effect.param1 + matrixFilterFrequency);
	fxParamTmp *= fxParamTmp;
	fxParam1 = ((fxParamTmp + 9.0f * fxParam1) * .1f);

	float OffsetTmp = fabsf(params.effect.param2);
	fxParam2 = ((OffsetTmp + 9.0f * fxParam2) * .1f);

	const float bipolarf = (fxParam1 - 0.5f);

	const float folded = fold(sigmoid(bipolarf * 7 * fxParam2)) * 4; // -1 < folded < 1

	const float offset = fxParam2 * fxParam2 * 0.17f;
	const float lrDelta = 0.005f * folded;

	const float range = 0.47f;

	const float f1L = clamp(fold((fxParam1 - offset - lrDelta) * range) * 2, filterWindowMin, filterWindowMax);
	const float f2L = clamp(fold((fxParam1 + offset + lrDelta) * range) * 2, filterWindowMin, filterWindowMax);
	const float f3L = clamp(fold((fxParam1 - (offset * 2) - lrDelta) * range) * 2, filterWindowMin, filterWindowMax);
	const float f4L = clamp(fold((fxParam1 + (offset * 2) + lrDelta) * range) * 2, filterWindowMin, filterWindowMax);
	float coef1L = (1.0f - f1L) / (1.0f + f1L);
	float coef2L = (1.0f - f2L) / (1.0f + f2L);
	float coef3L = (1.0f - f3L) / (1.0f + f3L);
	float coef4L = (1.0f - f4L) / (1.0f + f4L);
	const float f1R = clamp(fold((f1L - lrDelta) * range) * 2, filterWindowMin, filterWindowMax);
	const float f2R = clamp(fold((f2L + lrDelta) * range) * 2, filterWindowMin, filterWindowMax);
	const float f3R = clamp(fold((f3L - lrDelta) * range) * 2, filterWindowMin, filterWindowMax);
	const float f4R = clamp(fold((f4L + lrDelta) * range) * 2, filterWindowMin, filterWindowMax);
	float coef1R = (1.0f - f1R) / (1.0f + f1R);
	float coef2R = (1.0f - f2R) / (1.0f + f2R);
	float coef3R = (1.0f - f3R) / (1.0f + f3R);
	float coef4R = (1.0f - f4R) / (1.0f + f4R);

	float *sp = this->sampleBlock;

	float inmix;
	float _ly1L = v0L, _ly1R = v0R;
	float _ly2L = v1L, _ly2R = v1R;
	float _ly3L = v2L, _ly3R = v2R;
	float _ly4L = v3L, _ly4R = v3R;
	float _lx1L = v4L, _lx1R = v4R;
	float _lx2L = v5L, _lx2R = v5R;
	float _lx3L = v6L, _lx3R = v6R;
	float _lx4L = v7L, _lx4R = v7R;
	float _feedback = 0.08f;
	float _crossFeedback = 0.16f;
	float finalGain = mixerGain * 0.5f;

	for (int k = BLOCK_SIZE ; k--; ) {
		// Left voice
		inmix = (*sp) + _ly3L * _feedback - _ly2R * _crossFeedback;

		_ly1L = coef1L * (_ly1L + inmix) - _lx1L; // do 1st filter
		_lx1L = inmix;
		_ly2L = coef2L * (_ly2L + _ly1L) - _lx2L; // do 2nd filter
		_lx2L = _ly1L;
		_ly3L = coef3L * (_ly3L + _ly2L) - _lx3L; // do 3rd filter
		_lx3L = _ly2L;
		_ly4L = coef4L * (_ly4L + _ly3L) - _lx4L; // do 4th filter
		_lx4L = _ly3L;

		*sp++ = clamp((*sp + _ly4L) * finalGain, -ratioTimbres, ratioTimbres);

		// Right voice
		inmix = (*sp) + _ly3R * _feedback - _ly2L * _crossFeedback;

		_ly1R = coef1R * (_ly1R + inmix) - _lx1R; // do 1st filter
		_lx1R = inmix;
		_ly2R = coef2R * (_ly2R + _ly1R) - _lx2R; // do 2nd filter
		_lx2R = _ly1R;
		_ly3R = coef3R * (_ly3R + _ly2R) - _lx3R; // do 3rd filter
		_lx3R = _ly2R;
		_ly4R = coef4R * (_ly4R + _ly3R) - _lx4R; // do 4th filter
		_lx4R = _ly3R;

		*sp++ = clamp((*sp + _ly4R) * finalGain, -ratioTimbres, ratioTimbres);
	}

	v0L = _ly1L; v0R = _ly1R;
	v1L = _ly2L; v1R = _ly2R;
	v2L = _ly3L; v2R = _ly3R;
	v3L = _ly4L; v3R = _ly4R;
	v4L = _lx1L; v4R = _lx1R;
	v5L = _lx2L; v5R = _lx2R;
	v6L = _lx3L; v6R = _lx3R;
	v7L = _lx4L; v7R = _lx4R;
}
break;
case FILTER_AP4B :
{
	float fxParamTmp = (params.effect.param1 + matrixFilterFrequency);
	fxParamTmp *= fxParamTmp;
	fxParam1 = ((fxParamTmp + 9.0f * fxParam1) * .1f);
	
	float OffsetTmp = fabsf(params.effect.param2);
	fxParam2 = ((OffsetTmp + 9.0f * fxParam2) * .1f);

	const float bipolarf = (fxParam1 - 0.5f);
	const float folded = fold(sigmoid(bipolarf * 19 * fxParam2)) * 4; // -1 < folded < 1

	const float offset = fxParam2 * fxParam2 * 0.17f;
	const float lrDelta = 0.005f * folded;

	const float range = 0.47f;

	const float f1L = clamp(fold((fxParam1 - offset - lrDelta) * range) * 2, filterWindowMin, filterWindowMax);
	const float f2L = clamp(fold((fxParam1 + offset + lrDelta) * range) * 2, filterWindowMin, filterWindowMax);
	const float f3L = clamp(fold((fxParam1 - (offset * 2) - lrDelta) * range) * 2, filterWindowMin, filterWindowMax);
	const float f4L = clamp(fold((fxParam1 + (offset * 2) + lrDelta) * range) * 2, filterWindowMin, filterWindowMax);
	float coef1L = (1.0f - f1L) / (1.0f + f1L);
	float coef2L = (1.0f - f2L) / (1.0f + f2L);
	float coef3L = (1.0f - f3L) / (1.0f + f3L);
	float coef4L = (1.0f - f4L) / (1.0f + f4L);
	const float f1R = clamp(fold((fxParam1 - offset + lrDelta) * range) * 2, filterWindowMin, filterWindowMax);
	const float f2R = clamp(fold((fxParam1 + offset - lrDelta) * range) * 2, filterWindowMin, filterWindowMax);
	const float f3R = clamp(fold((fxParam1 - (offset * 2) + lrDelta) * range) * 2, filterWindowMin, filterWindowMax);
	const float f4R = clamp(fold((fxParam1 + (offset * 2) - lrDelta) * range) * 2, filterWindowMin, filterWindowMax);
	float coef1R = (1.0f - f1R) / (1.0f + f1R);
	float coef2R = (1.0f - f2R) / (1.0f + f2R);
	float coef3R = (1.0f - f3R) / (1.0f + f3R);
	float coef4R = (1.0f - f4R) / (1.0f + f4R);

	float *sp = this->sampleBlock;

	float _ly1L = v0L, _ly1R = v0R;
	float _ly2L = v1L, _ly2R = v1R;
	float _ly3L = v2L, _ly3R = v2R;
	float _ly4L = v3L, _ly4R = v3R;
	float _lx1L = v4L, _lx1R = v4R;
	float _lx2L = v5L, _lx2R = v5R;
	float _lx3L = v6L, _lx3R = v6R;
	float _lx4L = v7L, _lx4R = v7R;

	float _feedback = 0.68f;
	float _crossFeedback = 0.17f;
	float inmix;
	float finalGain = mixerGain * 0.5f;

	for (int k = BLOCK_SIZE ; k--; ) {
		// Left voice
		inmix = (*sp) - _feedback * _ly3L + _crossFeedback * _ly3R;

		_ly1L = coef1L * (_ly1L + inmix) - _lx1L; // do 1st filter
		_lx1L = inmix;
		_ly2L = coef2L * (_ly2L + _ly1L) - _lx2L; // do 2nd filter
		_lx2L = _ly1L;
		_ly3L = coef3L * (_ly3L + _ly2L) - _lx3L; // do 3rd filter
		_lx3L = _ly2L;
		_ly4L = coef4L * (_ly4L + _ly3L) - _lx4L; // do 4nth filter
		_lx4L = _ly3L;

		*sp++ = clamp((*sp + _ly4L) * finalGain, -ratioTimbres, ratioTimbres);

		// Right voice
		inmix = (*sp) - _feedback * _ly3R + _crossFeedback * _ly3L;

		_ly1R = coef1R * (_ly1R + inmix) - _lx1R; // do 1st filter
		_lx1R = inmix;
		_ly2R = coef2R * (_ly2R + _ly1R) - _lx2R; // do 2nd filter
		_lx2R = _ly1R;
		_ly3R = coef3R * (_ly3R + _ly2R) - _lx3R; // do 3rd filter
		_lx3R = _ly2R;
		_ly4R = coef4R * (_ly4R + _ly3R) - _lx4R; // do 4nth filter
		_lx4R = _ly3R;

		*sp++ = clamp((*sp + _ly4R) * finalGain, -ratioTimbres, ratioTimbres);
	}

	v0L = _ly1L; v0R = _ly1R;
	v1L = _ly2L; v1R = _ly2R;
	v2L = _ly3L; v2R = _ly3R;
	v3L = _ly4L; v3R = _ly4R;
	v4L = _lx1L; v4R = _lx1R;
	v5L = _lx2L; v5R = _lx2R;
	v6L = _lx3L; v6R = _lx3R;
	v7L = _lx4L; v7R = _lx4R;
}
break;
case FILTER_AP4D :
{
	float fxParamTmp = (params.effect.param1 + matrixFilterFrequency);
	const uint_fast8_t random = (*(uint_fast8_t *)noise) & 0xff;
	float randomF = (float)random * 0.00390625f;
	if (random < 76) {
		fxParam1 += (randomF * 0.002f) - 0.001f;
	}
	fxParamTmp *= fxParamTmp;
	fxParam1 = ((fxParamTmp + 9.0f * fxParam1) * .1f);
	
	float OffsetTmp = fabsf(params.effect.param2);
	fxParam2 = ((OffsetTmp + 9.0f * fxParam2) * .1f);

	const float offset = fxParam2 * fxParam2 * 0.17f;

	const float range1 = 0.33f;
	const float range2 = 0.14f;
	const float range3 = 0.05f;

	const float lowlimit = 0.027f;

	const float f1 = clamp(((lowlimit + fxParam1 + offset) * range1), filterWindowMin, filterWindowMax);
	const float f2 = clamp(((lowlimit + fxParam1 - offset) * range2), filterWindowMin, filterWindowMax);
	const float f3 = clamp(((lowlimit + fxParam1 + offset) * range3), filterWindowMin, filterWindowMax);
	float coef1 = (1.0f - f1) / (1.0f + f1);
	float coef2 = (1.0f - f2) / (1.0f + f2);
	float coef3 = (1.0f - f3) / (1.0f + f3);


	float *sp = this->sampleBlock;

	float _ly1L = v0L, _ly1R = v0R;
	float _ly2L = v1L, _ly2R = v1R;
	float _ly3L = v2L, _ly3R = v2R;
	float _ly4L = v3L, _ly4R = v3R;
	float _lx1L = v4L, _lx1R = v4R;
	float _lx2L = v5L, _lx2R = v5R;
	float _lx3L = v6L, _lx3R = v6R;
	float _lx4L = v7L, _lx4R = v7R;

	float _feedback = 0.15f + (randomF * 0.01) - 0.005f;
	float inmix;
	float finalGain = mixerGain * 0.5f;

	const float a = 0.85f;
	const float b = 1.f - a;

	const float f = 0.33f + f1;

	coef3 = clamp( coef3 + (*sp * 0.0075f), 0, 1);//nested f xmod

	for (int k = BLOCK_SIZE ; k--; ) {
		// Left voice
		inmix = (*sp) + _feedback * _ly4L;
		_ly1L = coef1 * (_ly1L + inmix) - _lx1L; // do 1st filter
		_lx1L = inmix;
		_ly2L = coef2 * (_ly3L + _ly1L) - _lx2L; // do 2nd filter
		_lx2L = _ly1L;
		_ly3L = _lx4L * (_ly3L + _ly2L) - _lx3L; // nested filter
		_lx3L = _ly2L;

		_lx4L = (_lx4L * 31 + coef3) * 0.03125f;// xmod damp

		_ly4L = (_ly3L * b) + (_ly4L * a); // lowpass

		*sp++ = clamp((_ly1L + _ly2L - *sp) * finalGain, -ratioTimbres, ratioTimbres);

		// Right voice
		inmix = (*sp) + _feedback * _ly4R;
		_ly1R = coef1 * (_ly1R + inmix) - _lx1R; // do 1st filter
		_lx1R = inmix;
		_ly2R = coef2 * (_ly3R + _ly1R) - _lx2R; // do 2nd filter
		_lx2R = _ly1R;
		_ly3R = _lx4R * (_ly3R + _ly2R) - _lx3R; // nested filter
		_lx3R = _ly2R;

		_lx4R = (_lx4R * 31 + coef3) * 0.03125f;// xmod damp

		_ly4R = (_ly3R * b) + (_ly4R * a); // lowpass

		*sp++ = clamp((_ly1R + _ly2R - *sp) * finalGain, -ratioTimbres, ratioTimbres);
	}

	v0L = _ly1L; v0R = _ly1R;
	v1L = _ly2L; v1R = _ly2R;
	v2L = _ly3L; v2R = _ly3R;
	v3L = _ly4L; v3R = _ly4R;
	v4L = _lx1L; v4R = _lx1R;
	v5L = _lx2L; v5R = _lx2R;
	v6L = _lx3L; v6R = _lx3R;
	v7L = _lx4L; v7R = _lx4R;
}
break;
case FILTER_ORYX:
	{
	//https://www.musicdsp.org/en/latest/Filters/23-state-variable.html
	float fxParamTmp = params.effect.param1 + matrixFilterFrequency;
	fxParamTmp *= fxParamTmp;
	// Low pass... on the Frequency
	fxParamTmp = (fold((fxParamTmp - 0.5f) * 0.25f) + 0.25f) * 2;
	fxParam1 = clamp((fxParamTmp + 9.0f * fxParam1) * .1f, 0, 1);

	float param2Tmp = (params.effect.param2);
	fxParam2 = ((param2Tmp + 19.0f * fxParam2) * .05f);
	const float rootf = 0.011f + ((fxParam2 * fxParam2) - 0.005f) * 0.08f;
	const float frange = 0.14f;
	const float bipolarf = (fxParam1 - 0.5f);

	float f1 = rootf + sigmoidPos((fxParam1 > 0.5f) ? (1 - fxParam1) : fxParam1) * frange;
	/*//f1 = fold(sigmoid(((f1 - 0.5f) * (2/frange)) * 7 * fxParam2)) * 4; // -1 < folded < 1*/
	const float fb = 0.08f + fxParam1 * 0.01f + noise[0] * 0.002f;
	const float scale = sqrt3(fb);

	const float spread = 1 + (fxParam2 * 0.13f);

	const float fold2 = fold(0.125f + sigmoid(bipolarf * 21 * fxParam2) * frange ) + 0.25f;
	const float f2 = rootf + frange * 1.15f + sigmoidPos(1 - fxParam1 + fold2 * 0.25f) * spread * frange * 1.25f;
	const float fb2 = 0.21f - fold2 * 0.08f - noise[1] * 0.0015f;
	const float scale2 = sqrt3(fb2);

	float *sp = this->sampleBlock;
	float lowL = v0L, bandL = v1L;
	float lowR = v0R, bandR = v1R;

	float lowL2 = v2L, bandL2 = v3L;
	float lowR2 = v2R, bandR2 = v3R;

	float lowL3 = v4L, lowL3b = v5L;
	float lowR3 = v4R, lowR3b = v5R;

	const float svfGain = (1 + SVFGAINOFFSET) * mixerGain;
	
	const float fap1 = clamp(f1, filterWindowMin, filterWindowMax);
	float coef1 = (1.0f - fap1) / (1.0f + fap1);

	float out;
	const float r = 0.985f;
	float nz;
	float drift = v6L;
	float nexDrift = noise[7] * 0.0005f;
	float deltaD = (nexDrift - drift) * 0.03125f;

	const float sat = 1.25f;

	for (int k=BLOCK_SIZE ; k--; ) {
		nz = noise[k] * 0.005f;

		// ----------- Left voice
		*sp = ((lowL + ((-lowL + *sp) * (r + nz))));
		// bandpass 1
		lowL += f1 * bandL;
		bandL += f1 * (scale * sat66(*sp * sat) - lowL - (fb + nz - drift) * bandL);

		// bandpass 2
		lowL2 += f2 * bandL2;
		bandL2 += f2 * (scale2 * *sp - lowL2 - fb2 * bandL2);

		out = bandL + bandL2;

		*sp++ = clamp(out * svfGain, -ratioTimbres, ratioTimbres);

		// ----------- Right voice
		*sp = ((lowR + ((-lowR + *sp) * (r - nz)))) ;
		// bandpass 1
		lowR += f1 * bandR;
		bandR += f1 * (scale * sat66(*sp * sat) - lowR - (fb - nz + drift) * bandR);

		// bandpass 2
		lowR2 += f2 * bandR2;
		bandR2 += f2 * (scale2 * *sp - lowR2 - fb2 * bandR2);

		out = bandR + bandR2;

		*sp++ = clamp(out * svfGain, -ratioTimbres, ratioTimbres);

		drift += deltaD;
	}

	v0L = lowL;
	v1L = bandL;
	v0R = lowR;
	v1R = bandR;
	
	v2L = lowL2;
	v3L = bandL2;
	v2R = lowR2;
	v3R = bandR2;

	v4L = lowL3;
	v5L = lowL3b;
	v4R = lowR3;
	v5R = lowR3b;

	v6L = nexDrift;
}
break;
case FILTER_ORYX2:
	{
	//https://www.musicdsp.org/en/latest/Filters/23-state-variable.html
	float fxParamTmp = params.effect.param1 + matrixFilterFrequency;
	fxParamTmp *= fxParamTmp;
	// Low pass... on the Frequency
	fxParamTmp = (fold((fxParamTmp - 0.5f) * 0.25f) + 0.25f) * 2;
	fxParam1 = clamp((fxParamTmp + 9.0f * fxParam1) * .1f, 0, 1);

	float param2Tmp = (params.effect.param2);
	fxParam2 = ((param2Tmp + 19.0f * fxParam2) * .05f);
	const float rootf = 0.031f + (fxParam2) * 0.0465f;
	const float frange = 0.22f;
	const float bipolarf = sigmoid(fxParam1 - 0.5f);

	const float f1 = rootf + sigmoidPos((fxParam1 > 0.55f) ? (0.7f - (fxParam1 * 0.7f)) : (fxParam1 * fxParam1)) * frange;
	const float fb = 0.074f + fxParam1 * 0.01f + noise[0] * 0.002f;
	const float scale = sqrt3(fb);

	const float spread = 1 + (fxParam2 * 0.13f);

	const float fold2 = fold(0.125f + sigmoid(bipolarf * 21 * fxParam2) * frange ) + 0.25f;
	const float f2 = rootf + frange * 1.1f - (sigmoidPos(fxParam1 + fold2 * 0.25f) - 0.5f) * spread * frange * 0.5f;
	const float fb2 = 0.11f - f1 * fold2 * 0.4f - noise[1] * 0.0015f;
	const float scale2 = sqrt3(fb2);

	const float fold3 = fold(sigmoid(bipolarf * 17 * fxParam2) * frange);
	const float f3 = rootf + frange * 1.35f - tanh3(((1 - fxParam1) * 2 - fold3 * 0.2f)) * spread * frange * 0.25f;
	const float fb3 = 0.13f - f1 * fold3 * 0.5f - noise[2] * 0.001f;
	const float scale3 = sqrt3(fb3);

	float *sp = this->sampleBlock;
	float lowL = v0L, bandL = v1L;
	float lowR = v0R, bandR = v1R;

	float lowL2 = v2L, bandL2 = v3L;
	float lowR2 = v2R, bandR2 = v3R;

	float lowL3 = v4L, bandL3 = v5L;
	float lowR3 = v4R, bandR3 = v5R;

	const float svfGain = (1 + SVFGAINOFFSET) * mixerGain;
	
	const float fap1 = clamp(f1, filterWindowMin, filterWindowMax);
	float coef1 = (1.0f - fap1) / (1.0f + fap1);

	float out;
	const float r = 0.985f;
	float nz;
	float drift = v6L;
	float nexDrift = noise[7] * 0.004f;
	float deltaD = (nexDrift - drift) * 0.03125f;

	for (int k=BLOCK_SIZE ; k--; ) {
		nz = noise[k] * 0.016f;

		// ----------- Left voice
		*sp = lowL + ((-lowL + *sp) * (r + nz));
		// bandpass 1
		lowL += f1 * bandL;
		bandL += f1 * (scale * *sp - lowL - (fb + nz - drift) * bandL);

		// bandpass 2
		lowL2 += (f2 + drift) * bandL2;
		bandL2 += f2 * (scale2 * *sp - lowL2 - fb2 * bandL2);

		// bandpass 3
		lowL3 += f3 * bandL3;
		bandL3 += f3 * (scale3 * *sp - lowL3 - fb3 * bandL3);

		out = (bandL) + (bandL2 + bandL3);

		*sp++ = clamp(out * svfGain, -ratioTimbres, ratioTimbres);

		// ----------- Right voice
		*sp = lowR + ((-lowR + *sp) * (r - nz));
		// bandpass 1
		lowR += f1 * bandR;
		bandR += f1 * (scale * *sp - lowR - (fb - nz + drift) * bandR);

		// bandpass 2
		lowR2 += (f2 + drift) * bandR2;
		bandR2 += f2 * (scale2 * *sp - lowR2 - fb2 * bandR2);

		// bandpass 3
		lowR3 += f3 * bandR3;
		bandR3 += f3 * (scale3 * *sp - lowR3 - fb3 * bandR3);

		out = (bandR) + (bandR2 + bandR3);

		*sp++ = clamp(out * svfGain, -ratioTimbres, ratioTimbres);

		drift += deltaD;
	}

	v0L = lowL;
	v1L = bandL;
	v0R = lowR;
	v1R = bandR;
	
	v2L = lowL2;
	v3L = bandL2;
	v2R = lowR2;
	v3R = bandR2;

	v4L = lowL3;
	v5L = bandL3;
	v4R = lowR3;
	v5R = bandR3;

	v6L = nexDrift;
}
break;
case FILTER_ORYX3:
{
//https://www.musicdsp.org/en/latest/Filters/23-state-variable.html
	float fxParamTmp = params.effect.param1 + matrixFilterFrequency;
	fxParamTmp *= fxParamTmp;
	// Low pass... on the Frequency
	fxParamTmp = (fold((fxParamTmp - 0.5f) * 0.25f) + 0.25f) * 2;
	fxParam1 = clamp((fxParamTmp + 9.0f * fxParam1) * .1f, 0, 1);

	float param2Tmp = (params.effect.param2);
	fxParam2 = ((param2Tmp + 19.0f * fxParam2) * .05f);
	const float rootf = 0.011f + ((fxParam2 * fxParam2) - 0.005f) * 0.08f;
	const float frange = 0.14f;
	const float bipolarf = (fxParam1 - 0.5f);

	float f1 = rootf + sigmoidPos((fxParam1 > 0.4f) ? (0.5f - fxParam1 * 0.25f) : fxParam1) * frange;
	const float fb = 0.08f + fxParam1 * 0.01f + noise[0] * 0.002f;
	const float scale = sqrt3(fb);

	const float spread = 1 + (fxParam2 * 0.13f);

	const float fold2 = fold(0.125f + sigmoid(bipolarf * 21 * fxParam2) * frange ) + 0.25f;
	const float f2 = rootf + frange * 1.15f + sigmoidPos(0.25f + 0.5f * fxParam1 + fold2 * 0.25f) * spread * frange * 1.25f;
	const float fb2 = 0.21f - fold2 * 0.08f - noise[1] * 0.0015f;
	const float scale2 = sqrt3(fb2);

	float *sp = this->sampleBlock;
	float lowL = v0L, bandL = v1L;
	float lowR = v0R, bandR = v1R;

	float lowL2 = v2L, bandL2 = v3L;
	float lowR2 = v2R, bandR2 = v3R;

	float lowL3 = v4L, lowL3b = v5L;
	float lowR3 = v4R, lowR3b = v5R;

	const float svfGain = (1 + SVFGAINOFFSET) * mixerGain;
	
	const float fap1 = clamp(f1, filterWindowMin, filterWindowMax);
	float coef1 = (1.0f - fap1) / (1.0f + fap1);

	float out;
	const float r = 0.985f;
	float nz;
	float drift = v6L;
	float nexDrift = noise[7] * 0.0006f;
	float deltaD = (nexDrift - drift) * 0.03125f;

	//const float sat = 1.25f;
	const int pos = (int)(0.375f * 2060);
	float drive = 0.2f;// - fxParam1 * fxParam1 * 0.25f;

	for (int k=BLOCK_SIZE ; k--; ) {
		nz = noise[k] * 0.005f;

		// ----------- Left voice
		*sp = ((lowL + ((-lowL + *sp) * (r + nz))));
		*sp = satSin(*sp, drive, pos);
		// bandpass 1
		lowL += f1 * bandL;
		bandL += f1 * (scale * *sp - lowL - (fb + nz - drift) * bandL);

		// bandpass 2
		lowL2 += f2 * bandL2;
		bandL2 += f2 * (scale2 * *sp - lowL2 - fb2 * bandL2);

		out = bandL + bandL2;

		*sp++ = clamp(out * svfGain, -ratioTimbres, ratioTimbres);

		// ----------- Right voice
		*sp = ((lowR + ((-lowR + *sp) * (r - nz)))) ;
		*sp = satSin(*sp, drive, pos);
		// bandpass 1
		lowR += f1 * bandR;
		bandR += f1 * (scale * *sp - lowR - (fb - nz + drift) * bandR);

		// bandpass 2
		lowR2 += f2 * bandR2;
		bandR2 += f2 * (scale2 * *sp - lowR2 - fb2 * bandR2);

		out = bandR + bandR2;

		*sp++ = clamp(out * svfGain, -ratioTimbres, ratioTimbres);

		drift += deltaD;
	}

	v0L = lowL;
	v1L = bandL;
	v0R = lowR;
	v1R = bandR;
	
	v2L = lowL2;
	v3L = bandL2;
	v2R = lowR2;
	v3R = bandR2;

	v4L = lowL3;
	v5L = lowL3b;
	v4R = lowR3;
	v5R = lowR3b;

	v6L = nexDrift;
}
break;
case FILTER_18DB:
{
	//https://www.musicdsp.org/en/latest/Filters/26-moog-vcf-variation-2.html
	float fxParamTmp = (params.effect.param1 + matrixFilterFrequency);
	fxParamTmp *= fxParamTmp;

	fxParam1 = clamp((fxParamTmp + 9.0f * fxParam1) * .1f, 0 , 1);
	float cut = clamp(sqrt3(fxParam1), filterWindowMin, 1);
	float cut2 = cut * cut;
	float attn = 0.37013f * cut2 * cut2;
	float inAtn = 0.3f;


	float OffsetTmp = fabsf(params.effect.param2);
	fxParam2 = ((OffsetTmp + 9.0f * fxParam2) * .1f);
	float res = fxParam2 * 6 + cut2 * 0.68f;
 	float fb = res * (1 - 0.178f * (cut2 + (1 + fxParam1 * fxParam1 * 0.5f) * fxParam2 * 0.333333f));
	float invCut = 1 - cut;

	//const float r = 0.985f;
	const float bipolarf = fxParam1 - 0.5f;
	const float fold3 = (fold(13 * bipolarf) + 0.125f) * 1.5f;
	float dc  = cut2 * 0.1f;
	float *sp = this->sampleBlock;

	float buf1L = v0L, buf2L = v1L, buf3L = v2L;
	float buf1R = v0R, buf2R = v1R, buf3R = v2R;

	float buf1inL = v4L, buf2inL = v5L, buf3inL = v6L;
	float buf1inR = v4R, buf2inR = v5R, buf3inR = v6R;

	float _ly1L = v3L, _ly1R = v3R;
	float _lx1L = v7L, _lx1R = v7R;

	const float f1 = clamp(0.3f + cut * cut * 0.47f, filterWindowMin, filterWindowMax);
	float coef1 = (1.0f - f1) / (1.0f + f1);

	float finalGain = mixerGain * (1 + fxParam2 * 0.75f) * 2.27f;

	const float r = 0.987f;

	for (int k = BLOCK_SIZE ; k--; ) {

		// Left voice
		*sp = buf3L + ((-buf3L + *sp) * r);

		*sp = tanh4(*sp - (buf3L) * (fb));
		*sp *= attn;
		buf1L = (*sp) + inAtn * buf1inL + invCut * buf1L; // Pole 1
		buf1inL = (*sp);
		buf2L = (buf1L) + inAtn * buf2inL + invCut * buf2L; // Pole 2
		buf2inL = buf1L;
		buf3L = (buf2L) + inAtn * buf3inL + invCut * buf3L; // Pole 3
		buf3inL = buf2L;

		_ly1L = (coef1) * (_ly1L + buf3L) - _lx1L; // allpass
		_lx1L = buf3L;

		*sp++ = clamp(_ly1L * finalGain, -ratioTimbres, ratioTimbres);

		// Right voice
		*sp = buf3R + ((-buf3R + *sp) * r);

		*sp = tanh4(*sp - (buf3R) * (fb));
		*sp *= attn;
		buf1R = (*sp) + inAtn * buf1inR + invCut * buf1R; // Pole 1
		buf1inR = (*sp);
		buf2R = (buf1R) + inAtn * buf2inR + invCut * buf2R; // Pole 2
		buf2inR = buf1R;
		buf3R = (buf2R) + inAtn * buf3inR + invCut * buf3R; // Pole 3
		buf3inR = buf2R;

		_ly1R = (coef1)  * (_ly1R + buf3R) - _lx1R; // allpass
		_lx1R = buf3R;

		*sp++ = clamp(_ly1R * finalGain, -ratioTimbres, ratioTimbres);
	}

	v0L = buf1L;
	v1L = buf2L;
	v2L = buf3L;

	v0R = buf1R;
	v1R = buf2R;
	v2R = buf3R;

	v4L = buf1inL;
	v5L = buf2inL;
	v6L = buf3inL;

	v4R = buf1inR;
	v5R = buf2inR;
	v6R = buf3inR;

	v3L = _ly1L;
	v3R = _ly1R;
	v7L = _lx1L;
	v7R = _lx1R;

	break;
}
break;
case FILTER_LADDER:
{
	//https://www.musicdsp.org/en/latest/Filters/26-moog-vcf-variation-2.html
	float fxParamTmp = (params.effect.param1 + matrixFilterFrequency);
	fxParamTmp *= fxParamTmp;

	fxParam1 = clamp((fxParamTmp + 9.0f * fxParam1) * .1f, 0 , 1);
	float cut = clamp(sqrt3(fxParam1), filterWindowMin, 1);
	float cut2 = cut * cut;
	float attn = 0.35013f * cut2 * cut2;
	float inAtn = 0.3f;

	float OffsetTmp = fabsf(params.effect.param2);
	fxParam2 = ((OffsetTmp + 9.0f * fxParam2) * .1f);
	float res = fxParam2 * 4.5f * (0.8f + cut2 * 0.2f);
 	float fb = res * (1 - 0.15f * cut2);
	float invCut = 1 - cut;

	const float r = 0.985f;

	float *sp = this->sampleBlock;

	float buf1L = v0L, buf2L = v1L, buf3L = v2L, buf4L = v3L;
	float buf1R = v0R, buf2R = v1R, buf3R = v2R, buf4R = v3R;

	float buf1inL = v4L, buf2inL = v5L, buf3inL = v6L, buf4inL = v7L;
	float buf1inR = v4R, buf2inR = v5R, buf3inR = v6R, buf4inR = v7R;

	float finalGain = mixerGain * (1 + fxParam2 * 2);

	for (int k = BLOCK_SIZE ; k--; ) {

		// Left voice
		*sp = buf4L + ((-buf4L + *sp) * r);

		*sp -= tanh3(0.005f + buf4L) * (fb + buf4R * 0.05f);
		*sp *= attn;
		buf1L = *sp + inAtn * buf1inL + invCut * buf1L; // Pole 1
		buf1inL = *sp;
		buf2L = buf1L + inAtn * buf2inL + invCut * buf2L; // Pole 2
		buf2inL = buf1L;
		buf3L = buf2L + inAtn * buf3inL + invCut * buf3L; // Pole 3
		buf3inL = buf2L;
		buf4L = buf3L + inAtn * buf4inL + invCut * buf4L; // Pole 4
		buf4inL = buf3L;

		*sp++ = clamp(buf4L * finalGain, -ratioTimbres, ratioTimbres);

		// Right voice
		*sp = buf4R + ((-buf4R + *sp) * r);

		*sp -= tanh3(0.005f + buf4R) * (fb - buf4L * 0.05f);
		*sp *= attn;
		buf1R = *sp + inAtn * buf1inR + invCut * buf1R; // Pole 1
		buf1inR = *sp;
		buf2R = buf1R + inAtn * buf2inR + invCut * buf2R; // Pole 2
		buf2inR = buf1R;
		buf3R = buf2R + inAtn * buf3inR + invCut * buf3R; // Pole 3
		buf3inR = buf2R;
		buf4R = buf3R + inAtn * buf4inR + invCut * buf4R; // Pole 4
		buf4inR = buf3R;

		*sp++ = clamp(buf4R * finalGain, -ratioTimbres, ratioTimbres);
	}

	v0L = buf1L;
	v1L = buf2L;
	v2L = buf3L;
	v3L = buf4L;

	v0R = buf1R;
	v1R = buf2R;
	v2R = buf3R;
	v3R = buf4R;

	v4L = buf1inL;
	v5L = buf2inL;
	v6L = buf3inL;
	v7L = buf4inL;

	v4R = buf1inR;
	v5R = buf2inR;
	v6R = buf3inR;
	v7R = buf4inR;

	break;
}
case FILTER_LADDER2:
{
	//https://www.musicdsp.org/en/latest/Filters/240-karlsen-fast-ladder.html
	float fxParamTmp = (params.effect.param1 + matrixFilterFrequency);
	fxParamTmp *= fxParamTmp;

	fxParam1 = ((fxParamTmp + 9.0f * fxParam1) * .1f);
	float cut = clamp(sqrt3(fxParam1), filterWindowMin, filterWindowMax);

	float OffsetTmp = fabsf(params.effect.param2);
	fxParam2 = ((OffsetTmp + 9.0f * fxParam2) * .1f);
	float res = fxParam2;

	float *sp = this->sampleBlock;

	float buf1L = v0L, buf2L = v1L, buf3L = v2L, buf4L = v3L;
	float buf1R = v0R, buf2R = v1R, buf3R = v2R, buf4R = v3R;

	float _ly1L = v4L, _lx1L = v5L;
	float _ly1R = v4R, _lx1R = v5R;

	float _ly2L = v6L, _ly2R = v6R;
	float _lx2L = v7L, _lx2R = v7R;

	float resoclip;

	const float bipolarf = fxParam1 - 0.5f;
	const float fold3 = (fold(13 * bipolarf) + 0.125f) * 0.25f;
	const float f1 = clamp(0.33f + fold3 * (1 - cut * 0.5f), filterWindowMin, filterWindowMax);
	float coef1 = (1.0f - f1) / (1.0f + f1);
	const float f2 = clamp(f1 * f1, filterWindowMin, filterWindowMax);
	float coef2 = (1.0f - f2) / (1.0f + f2);

	float finalGain = mixerGain * 1.25f;
	float nz;

	for (int k = BLOCK_SIZE ; k--; ) {

		// Left voice
		*sp = *sp - sat25(0.025f + buf4L * (res + buf4R * 0.05f));
		buf1L = ((*sp - buf1L) * cut) + buf1L;
		buf2L = ((buf1L - buf2L) * cut) + buf2L;
		_ly1L = coef1 * (_ly1L + buf2L) - _lx1L; // allpass
		_lx1L = buf2L;
		buf3L = ((_ly1L - buf3L) * cut) + buf3L;
		_ly2L = coef2 * (_ly2L + buf3L) - _lx2L; // allpass
		_lx2L = buf3L;
		buf4L = ((_ly2L - buf4L) * cut) + buf4L;
		*sp++ = clamp(buf4L * finalGain, -ratioTimbres, ratioTimbres);

		// Right voice
		*sp = *sp - sat25(0.025f + buf4R * (res - buf4L * 0.05f));
		buf1R = ((*sp - buf1R) * cut) + buf1R;
		buf2R = ((buf1R - buf2R) * cut) + buf2R;
		_ly1R = coef1 * (_ly1R + buf2R) - _lx1R; // allpass
		_lx1R = buf2R;
		buf3R = ((_ly1R - buf3R) * cut) + buf3R;
		_ly2R = coef2 * (_ly2R + buf3R) - _lx2R; // allpass
		_lx2R = buf3R;
		buf4R = ((_ly2R - buf4R) * cut) + buf4R;
		*sp++ = clamp(buf4R * finalGain, -ratioTimbres, ratioTimbres);
	}

	v0L = buf1L;
	v1L = buf2L;
	v2L = buf3L;
	v3L = buf4L;

	v0R = buf1R;
	v1R = buf2R;
	v2R = buf3R;
	v3R = buf4R;

	v4L = _ly1L;
	v5L = _lx1L;
	v4R = _ly1R;
	v5R = _lx1R;

	v6L = _ly2L;
	v6R = _ly2R;
	v7L = _lx2L;
	v7R = _lx2R;

	break;
}
case FILTER_DIOD:
{
	float fxParamTmp = SVFOFFSET + params.effect.param1 + matrixFilterFrequency;
	fxParamTmp *= fxParamTmp;
	// Low pass... on the Frequency
	fxParam1 = clamp((fxParamTmp + 9.0f * fxParam1) * .1f, 0, 1);

	const float f = fxParam1 * fxParam1;
	const float fmeta = f * sigmoid(f);
	const float fb = sqrt3(0.7f - fxParam2 * 0.699f);
	const float scale = sqrt3(fb);

	float dc  = f * 0.05f * fb;
	const float f2 = 0.25f + f * 0.5f;

	float *sp = this->sampleBlock;
	float lowL = v0L, highL = 0, bandL = v1L;
	float lowR = v0R, highR = 0, bandR = v1R;

	const float svfGain = (1 + fxParam2 * fxParam2 * 0.75f) * mixerGain;

	float attn = 0.05f + 0.2f * f * f * f;
	float r = 0.985f;
	float hibp;

	for (int k = BLOCK_SIZE; k--;)	{
		// Left voice
		*sp = (lowL + ((-lowL + *sp) * r));

		hibp = attn * clamp(*sp - bandL, -ratioTimbres, ratioTimbres);

		lowL += fmeta * hibp;
		bandL += fmeta * (scale * *sp - lowL - fb * (hibp));

		lowL += f * bandL;
		bandL += f * (scale * (*sp + dc) - lowL - fb * (bandL));

		*sp++ = clamp(lowL * svfGain, -ratioTimbres, ratioTimbres);

		// Right voice
		*sp = (lowR + ((-lowR + *sp) * r));

		hibp = attn * clamp(*sp - bandR, -ratioTimbres, ratioTimbres);

		lowR += fmeta * hibp;
		bandR += fmeta * (scale * *sp - lowR - fb * (hibp));

		lowR += f * bandR;
		bandR += f * (scale * (*sp + dc) - lowR - fb * (bandR));

		*sp++ = clamp(lowR * svfGain, -ratioTimbres, ratioTimbres);
	}

	v0L = lowL;
	v1L = bandL;
	v0R = lowR;
	v1R = bandR;

}
break;
case FILTER_KRMG:
{
	//https://github.com/ddiakopoulos/MoogLadders/blob/master/src/KrajeskiModel.h
	float fxParamTmp = SVFOFFSET + params.effect.param1 + matrixFilterFrequency;
	fxParamTmp *= fxParamTmp;
	// Low pass... on the Frequency
	fxParam1 = clamp((fxParamTmp + 9.0f * fxParam1) * .1f, 0, 1);

	const float wc = 0.1f + fxParam1 * fxParam1;
	const float wc2 = wc * wc;
	const float wc3 = wc2 * wc;

	const float g = 0.9892f * wc - 0.4342f * wc2 + 0.1381f * wc3 - 0.0202f * wc2 * wc2;
	const float drive = 0.85f;
	const float gComp = 1;
	const float resonance = fxParam2 * 0.52f - fxParam1 * 0.05f;
	const float gRes = 1.5f * resonance * (1.0029f + 0.0526f * wc - 0.926f * wc2 + 0.0218f * wc3);

	float *sp = this->sampleBlock;
	float state0L = v0L, state1L = v1L, state2L = v2L, state3L = v3L, state4L = v4L;
	float delay0L = v5L, delay1L = v6L, delay2L = v7L, delay3L = v8L;

	float state0R = v0R, state1R = v1R, state2R = v2R, state3R = v3R, state4R = v4R;
	float delay0R = v5R, delay1R = v6R, delay2R = v7R, delay3R = v8R;

	const float va1 = 0.2307692308f;//0.3f / 1.3f;
	const float va2 = 0.7692307692f;//1 / 1.3f;
	float r = 0.989f;

	float drift = fxParamB2;
	float nz;
	float nexDrift = noise[7] * 0.015f;
	float deltaD = (nexDrift - drift) * 0.000625f;

	float finalGain = mixerGain * 0.87f;

	for (int k = BLOCK_SIZE; k--;)
	{
		nz = noise[k] * 0.0012f;
		// Left voice
		*sp = (state4L + ((-state4L + *sp) * r));
		state0L = tanh4((drive - drift  + nz) * (*sp - gRes * (state4L - gComp * *sp)));

		state1L = g * (va1 * state0L + va2 * delay0L - state1L) + state1L;
		delay0L = state0L;

		state2L = g * (va1 * state1L + va2 * delay1L - state2L) + state2L;
		delay1L = state1L;

		state3L = g * (va1 * state2L + va2 * delay2L - state3L) + state3L;
		delay2L = state2L;

		state4L = g * (va1 * state3L + va2 * delay3L - state4L) + state4L;
		delay3L = state3L;

		*sp++ = clamp(state4L * finalGain, -ratioTimbres, ratioTimbres);

		// Right voice
		*sp = (state4R + ((-state4R + *sp) * r));
		state0R = tanh4((drive + drift - nz) * (*sp - gRes * (state4R - gComp * *sp)));

		state1R = g * (va1 * state0R + va2 * delay0R - state1R) + state1R;
		delay0R = state0R;

		state2R = g * (va1 * state1R + va2 * delay1R - state2R) + state2R;
		delay1R = state1R;

		state3R = g * (va1 * state2R + va2 * delay2R - state3R) + state3R;
		delay2R = state2R;

		state4R = g * (va1 * state3R + va2 * delay3R - state4R) + state4R;
		delay3R = state3R;

		*sp++ = clamp(state4R * finalGain, -ratioTimbres, ratioTimbres);

		drift += deltaD;
	}

	v0L = state0L;
	v1L = state1L;
	v2L = state2L;
	v3L = state3L;
	v4L = state4L;

	v5L = delay0L;
	v6L = delay1L;
	v7L = delay2L;
	v8L = delay3L;

	v0R = state0R;
	v1R = state1R;
	v2R = state2R;
	v3R = state3R;
	v4R = state4R;

	v5R = delay0R;
	v6R = delay1R;
	v7R = delay2R;
	v8R = delay3R;

	fxParamB2 = nexDrift;
}
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
